svofski/videoconditioner/src/fir/filter/filter_0002_rtl.vhd

----------------------------------------------------------------------------- 
-- Altera DSP Builder Advanced Flow Tools Release Version 13.0sp1
-- Quartus II development tool and MATLAB/Simulink Interface
-- 
-- Legal Notice: Copyright 2013 Altera Corporation.  All rights reserved.    
-- Your use of  Altera  Corporation's design tools,  logic functions and other 
-- software and tools,  and its AMPP  partner logic functions, and  any output 
-- files  any of the  foregoing  device programming or simulation files),  and 
-- any associated  documentation or information are expressly subject  to  the 
-- terms and conditions  of the Altera Program License Subscription Agreement, 
-- Altera  MegaCore  Function  License  Agreement, or other applicable license 
-- agreement,  including,  without limitation,  that your use  is for the sole 
-- purpose of  programming  logic  devices  manufactured by Altera and sold by 
-- Altera or its authorized  distributors.  Please  refer  to  the  applicable 
-- agreement for further details.
----------------------------------------------------------------------------- 

-- VHDL created from filter_0002_rtl
-- VHDL created on Tue Aug 05 01:28:15 2014


library IEEE;
use IEEE.std_logic_1164.all;
use IEEE.NUMERIC_STD.all;
use IEEE.MATH_REAL.all;
use std.TextIO.all;
use work.dspba_library_package.all;

LIBRARY altera_mf;
USE altera_mf.altera_mf_components.all;
LIBRARY lpm;
USE lpm.lpm_components.all;

-- Text written from d:/SJ/nightly/13.0sp1/232/w32/p4/ip/aion/src/mip_common/hw_model.cpp:1303
entity filter_0002_rtl is
    port (
        xIn_v : in std_logic_vector(0 downto 0);
        xIn_c : in std_logic_vector(7 downto 0);
        xIn_0 : in std_logic_vector(6 downto 0);
        xOut_v : out std_logic_vector(0 downto 0);
        xOut_c : out std_logic_vector(7 downto 0);
        xOut_0 : out std_logic_vector(20 downto 0);
        clk : in std_logic;
        areset : in std_logic
        );
end;

architecture normal of filter_0002_rtl is

    attribute altera_attribute : string;
    attribute altera_attribute of normal : architecture is "-name NOT_GATE_PUSH_BACK OFF; -name PHYSICAL_SYNTHESIS_REGISTER_DUPLICATION ON; -name AUTO_SHIFT_REGISTER_RECOGNITION OFF; -name MESSAGE_DISABLE 10036; -name MESSAGE_DISABLE 10037; -name MESSAGE_DISABLE 14130; -name MESSAGE_DISABLE 14320; -name MESSAGE_DISABLE 15400; -name MESSAGE_DISABLE 14130; -name MESSAGE_DISABLE 10036; -name MESSAGE_DISABLE 12020; -name MESSAGE_DISABLE 12030; -name MESSAGE_DISABLE 12010; -name MESSAGE_DISABLE 12110; -name MESSAGE_DISABLE 14320; -name MESSAGE_DISABLE 13410";

    signal GND_q : std_logic_vector (0 downto 0);
    signal VCC_q : std_logic_vector (0 downto 0);
    signal d_u0_m0_wo0_memread_q_11_q : std_logic_vector (0 downto 0);
    signal d_u0_m0_wo0_memread_q_13_q : std_logic_vector (0 downto 0);
    signal d_u0_m0_wo0_memread_q_17_q : std_logic_vector (0 downto 0);
    signal u0_m0_wo0_wi0_delayr1_q : std_logic_vector (6 downto 0);
    signal u0_m0_wo0_wi0_delayr2_q : std_logic_vector (6 downto 0);
    signal u0_m0_wo0_wi0_delayr3_q : std_logic_vector (6 downto 0);
    signal u0_m0_wo0_wi0_delayr4_q : std_logic_vector (6 downto 0);
    signal d_u0_m0_wo0_wi0_delayr4_q_16_q : std_logic_vector (6 downto 0);
    signal u0_m0_wo0_wi0_delayr5_q : std_logic_vector (6 downto 0);
    signal d_u0_m0_wo0_wi0_delayr5_q_14_q : std_logic_vector (6 downto 0);
    signal u0_m0_wo0_wi0_delayr6_q : std_logic_vector (6 downto 0);
    signal d_u0_m0_wo0_wi0_delayr6_q_14_q : std_logic_vector (6 downto 0);
    signal u0_m0_wo0_wi0_delayr7_q : std_logic_vector (6 downto 0);
    signal d_u0_m0_wo0_wi0_delayr7_q_14_q : std_logic_vector (6 downto 0);
    signal u0_m0_wo0_wi0_delayr8_q : std_logic_vector (6 downto 0);
    signal d_u0_m0_wo0_wi0_delayr8_q_13_q : std_logic_vector (6 downto 0);
    signal u0_m0_wo0_wi0_delayr9_q : std_logic_vector (6 downto 0);
    signal d_u0_m0_wo0_wi0_delayr9_q_11_q : std_logic_vector (6 downto 0);
    signal u0_m0_wo0_wi0_delayr10_q : std_logic_vector (6 downto 0);
    signal d_u0_m0_wo0_wi0_delayr10_q_11_q : std_logic_vector (6 downto 0);
    signal u0_m0_wo0_wi0_delayr11_q : std_logic_vector (6 downto 0);
    signal d_u0_m0_wo0_wi0_delayr11_q_11_q : std_logic_vector (6 downto 0);
    signal u0_m0_wo0_wi0_delayr12_q : std_logic_vector (6 downto 0);
    signal d_u0_m0_wo0_wi0_delayr12_q_11_q : std_logic_vector (6 downto 0);
    signal u0_m0_wo0_wi0_delayr13_q : std_logic_vector (6 downto 0);
    signal d_u0_m0_wo0_wi0_delayr13_q_11_q : std_logic_vector (6 downto 0);
    signal u0_m0_wo0_wi0_delayr14_q : std_logic_vector (6 downto 0);
    signal u0_m0_wo0_wi0_delayr15_q : std_logic_vector (6 downto 0);
    signal d_u0_m0_wo0_wi0_delayr15_q_11_q : std_logic_vector (6 downto 0);
    signal u0_m0_wo0_wi0_delayr16_q : std_logic_vector (6 downto 0);
    signal d_u0_m0_wo0_wi0_delayr16_q_11_q : std_logic_vector (6 downto 0);
    signal u0_m0_wo0_wi0_delayr17_q : std_logic_vector (6 downto 0);
    signal d_u0_m0_wo0_wi0_delayr17_q_11_q : std_logic_vector (6 downto 0);
    signal u0_m0_wo0_wi0_delayr18_q : std_logic_vector (6 downto 0);
    signal d_u0_m0_wo0_wi0_delayr18_q_11_q : std_logic_vector (6 downto 0);
    signal u0_m0_wo0_wi0_delayr19_q : std_logic_vector (6 downto 0);
    signal d_u0_m0_wo0_wi0_delayr19_q_11_q : std_logic_vector (6 downto 0);
    signal u0_m0_wo0_wi0_delayr20_q : std_logic_vector (6 downto 0);
    signal d_u0_m0_wo0_wi0_delayr20_q_11_q : std_logic_vector (6 downto 0);
    signal u0_m0_wo0_wi0_delayr21_q : std_logic_vector (6 downto 0);
    signal d_u0_m0_wo0_wi0_delayr21_q_11_q : std_logic_vector (6 downto 0);
    signal u0_m0_wo0_wi0_delayr22_q : std_logic_vector (6 downto 0);
    signal d_u0_m0_wo0_wi0_delayr22_q_11_q : std_logic_vector (6 downto 0);
    signal u0_m0_wo0_wi0_delayr23_q : std_logic_vector (6 downto 0);
    signal d_u0_m0_wo0_wi0_delayr23_q_11_q : std_logic_vector (6 downto 0);
    signal u0_m0_wo0_wi0_delayr24_q : std_logic_vector (6 downto 0);
    signal d_u0_m0_wo0_wi0_delayr24_q_11_q : std_logic_vector (6 downto 0);
    signal u0_m0_wo0_wi0_delayr25_q : std_logic_vector (6 downto 0);
    signal d_u0_m0_wo0_wi0_delayr25_q_11_q : std_logic_vector (6 downto 0);
    signal u0_m0_wo0_wi0_delayr26_q : std_logic_vector (6 downto 0);
    signal u0_m0_wo0_wi0_delayr27_q : std_logic_vector (6 downto 0);
    signal d_u0_m0_wo0_wi0_delayr27_q_11_q : std_logic_vector (6 downto 0);
    signal u0_m0_wo0_wi0_delayr28_q : std_logic_vector (6 downto 0);
    signal d_u0_m0_wo0_wi0_delayr28_q_11_q : std_logic_vector (6 downto 0);
    signal u0_m0_wo0_wi0_delayr29_q : std_logic_vector (6 downto 0);
    signal d_u0_m0_wo0_wi0_delayr29_q_11_q : std_logic_vector (6 downto 0);
    signal u0_m0_wo0_wi0_delayr30_q : std_logic_vector (6 downto 0);
    signal d_u0_m0_wo0_wi0_delayr30_q_11_q : std_logic_vector (6 downto 0);
    signal u0_m0_wo0_wi0_delayr31_q : std_logic_vector (6 downto 0);
    signal d_u0_m0_wo0_wi0_delayr31_q_11_q : std_logic_vector (6 downto 0);
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

	--u0_m0_wo0_mtree_mult1_34_shift0(BITSHIFT,187)@14
    u0_m0_wo0_mtree_mult1_34_shift0_q_int <= d_u0_m0_wo0_wi0_delayr6_q_14_q & "00";
    u0_m0_wo0_mtree_mult1_34_shift0_q <= u0_m0_wo0_mtree_mult1_34_shift0_q_int(8 downto 0);

	--u0_m0_wo0_mtree_add0_17(ADD,147)@14
    u0_m0_wo0_mtree_add0_17_a <= STD_LOGIC_VECTOR((9 downto 9 => u0_m0_wo0_mtree_mult1_34_shift0_q(8)) & u0_m0_wo0_mtree_mult1_34_shift0_q);
    u0_m0_wo0_mtree_add0_17_b <= STD_LOGIC_VECTOR((9 downto 8 => u0_m0_wo0_mtree_mult1_35_shift0_q(7)) & u0_m0_wo0_mtree_mult1_35_shift0_q);
    u0_m0_wo0_mtree_add0_17: PROCESS (clk, areset)
    BEGIN
        IF (areset = '1') THEN
            u0_m0_wo0_mtree_add0_17_o <= (others => '0');
        ELSIF(clk'EVENT AND clk = '1') THEN
            u0_m0_wo0_mtree_add0_17_o <= STD_LOGIC_VECTOR(SIGNED(u0_m0_wo0_mtree_add0_17_a) + SIGNED(u0_m0_wo0_mtree_add0_17_b));
        END IF;
    END PROCESS;
    u0_m0_wo0_mtree_add0_17_q <= u0_m0_wo0_mtree_add0_17_o(9 downto 0);


	--u0_m0_wo0_wi0_delayr7(DELAY,14)@10
    u0_m0_wo0_wi0_delayr7 : dspba_delay
    GENERIC MAP ( width => 7, depth => 1 )
    PORT MAP ( xin => u0_m0_wo0_wi0_delayr6_q, xout => u0_m0_wo0_wi0_delayr7_q, ena => xIn_v(0), clk => clk, aclr => areset );

	--d_u0_m0_wo0_wi0_delayr7_q_14(DELAY,300)@10
    d_u0_m0_wo0_wi0_delayr7_q_14 : dspba_delay
    GENERIC MAP ( width => 7, depth => 4 )
    PORT MAP ( xin => u0_m0_wo0_wi0_delayr7_q, xout => d_u0_m0_wo0_wi0_delayr7_q_14_q, clk => clk, aclr => areset );

	--u0_m0_wo0_mtree_mult1_33_shift0(BITSHIFT,188)@14
    u0_m0_wo0_mtree_mult1_33_shift0_q_int <= d_u0_m0_wo0_wi0_delayr7_q_14_q & "000";
    u0_m0_wo0_mtree_mult1_33_shift0_q <= u0_m0_wo0_mtree_mult1_33_shift0_q_int(9 downto 0);

	--u0_m0_wo0_mtree_mult1_32_shift0(BITSHIFT,189)@13
    u0_m0_wo0_mtree_mult1_32_shift0_q_int <= d_u0_m0_wo0_wi0_delayr8_q_13_q & "0";
    u0_m0_wo0_mtree_mult1_32_shift0_q <= u0_m0_wo0_mtree_mult1_32_shift0_q_int(7 downto 0);

	--u0_m0_wo0_wi0_delayr8(DELAY,15)@10
    u0_m0_wo0_wi0_delayr8 : dspba_delay
    GENERIC MAP ( width => 7, depth => 1 )
    PORT MAP ( xin => u0_m0_wo0_wi0_delayr7_q, xout => u0_m0_wo0_wi0_delayr8_q, ena => xIn_v(0), clk => clk, aclr => areset );

	--d_u0_m0_wo0_wi0_delayr8_q_13(DELAY,301)@10
    d_u0_m0_wo0_wi0_delayr8_q_13 : dspba_delay
    GENERIC MAP ( width => 7, depth => 3 )
    PORT MAP ( xin => u0_m0_wo0_wi0_delayr8_q, xout => d_u0_m0_wo0_wi0_delayr8_q_13_q, clk => clk, aclr => areset );

	--u0_m0_wo0_mtree_mult1_32_add_1(ADD,190)@13
    u0_m0_wo0_mtree_mult1_32_add_1_a <= STD_LOGIC_VECTOR((8 downto 7 => d_u0_m0_wo0_wi0_delayr8_q_13_q(6)) & d_u0_m0_wo0_wi0_delayr8_q_13_q);
    u0_m0_wo0_mtree_mult1_32_add_1_b <= STD_LOGIC_VECTOR((8 downto 8 => u0_m0_wo0_mtree_mult1_32_shift0_q(7)) & u0_m0_wo0_mtree_mult1_32_shift0_q);
    u0_m0_wo0_mtree_mult1_32_add_1: PROCESS (clk, areset)
    BEGIN
        IF (areset = '1') THEN
            u0_m0_wo0_mtree_mult1_32_add_1_o <= (others => '0');
        ELSIF(clk'EVENT AND clk = '1') THEN
            u0_m0_wo0_mtree_mult1_32_add_1_o <= STD_LOGIC_VECTOR(SIGNED(u0_m0_wo0_mtree_mult1_32_add_1_a) + SIGNED(u0_m0_wo0_mtree_mult1_32_add_1_b));
        END IF;
    END PROCESS;
    u0_m0_wo0_mtree_mult1_32_add_1_q <= u0_m0_wo0_mtree_mult1_32_add_1_o(8 downto 0);


	--u0_m0_wo0_mtree_mult1_32_shift2(BITSHIFT,191)@14
    u0_m0_wo0_mtree_mult1_32_shift2_q_int <= u0_m0_wo0_mtree_mult1_32_add_1_q & "00";
    u0_m0_wo0_mtree_mult1_32_shift2_q <= u0_m0_wo0_mtree_mult1_32_shift2_q_int(10 downto 0);

	--u0_m0_wo0_mtree_add0_16(ADD,146)@14
    u0_m0_wo0_mtree_add0_16_a <= STD_LOGIC_VECTOR((11 downto 11 => u0_m0_wo0_mtree_mult1_32_shift2_q(10)) & u0_m0_wo0_mtree_mult1_32_shift2_q);
    u0_m0_wo0_mtree_add0_16_b <= STD_LOGIC_VECTOR((11 downto 10 => u0_m0_wo0_mtree_mult1_33_shift0_q(9)) & u0_m0_wo0_mtree_mult1_33_shift0_q);
    u0_m0_wo0_mtree_add0_16: PROCESS (clk, areset)
    BEGIN
        IF (areset = '1') THEN
            u0_m0_wo0_mtree_add0_16_o <= (others => '0');
        ELSIF(clk'EVENT AND clk = '1') THEN
            u0_m0_wo0_mtree_add0_16_o <= STD_LOGIC_VECTOR(SIGNED(u0_m0_wo0_mtree_add0_16_a) + SIGNED(u0_m0_wo0_mtree_add0_16_b));
        END IF;
    END PROCESS;
    u0_m0_wo0_mtree_add0_16_q <= u0_m0_wo0_mtree_add0_16_o(11 downto 0);


	--u0_m0_wo0_mtree_add1_8(ADD,158)@15
    u0_m0_wo0_mtree_add1_8_a <= STD_LOGIC_VECTOR((13 downto 12 => u0_m0_wo0_mtree_add0_16_q(11)) & u0_m0_wo0_mtree_add0_16_q);
    u0_m0_wo0_mtree_add1_8_b <= STD_LOGIC_VECTOR((13 downto 10 => u0_m0_wo0_mtree_add0_17_q(9)) & u0_m0_wo0_mtree_add0_17_q);
    u0_m0_wo0_mtree_add1_8: PROCESS (clk, areset)
    BEGIN
        IF (areset = '1') THEN
            u0_m0_wo0_mtree_add1_8_o <= (others => '0');
        ELSIF(clk'EVENT AND clk = '1') THEN
            u0_m0_wo0_mtree_add1_8_o <= STD_LOGIC_VECTOR(SIGNED(u0_m0_wo0_mtree_add1_8_a) + SIGNED(u0_m0_wo0_mtree_add1_8_b));
        END IF;
    END PROCESS;
    u0_m0_wo0_mtree_add1_8_q <= u0_m0_wo0_mtree_add1_8_o(13 downto 0);


	--u0_m0_wo0_mtree_add2_4(ADD,164)@16
    u0_m0_wo0_mtree_add2_4_a <= STD_LOGIC_VECTOR((14 downto 14 => u0_m0_wo0_mtree_add1_8_q(13)) & u0_m0_wo0_mtree_add1_8_q);
    u0_m0_wo0_mtree_add2_4_b <= STD_LOGIC_VECTOR((14 downto 7 => d_u0_m0_wo0_wi0_delayr4_q_16_q(6)) & d_u0_m0_wo0_wi0_delayr4_q_16_q);
    u0_m0_wo0_mtree_add2_4: PROCESS (clk, areset)
    BEGIN
        IF (areset = '1') THEN
            u0_m0_wo0_mtree_add2_4_o <= (others => '0');
        ELSIF(clk'EVENT AND clk = '1') THEN
            u0_m0_wo0_mtree_add2_4_o <= STD_LOGIC_VECTOR(SIGNED(u0_m0_wo0_mtree_add2_4_a) + SIGNED(u0_m0_wo0_mtree_add2_4_b));
        END IF;
    END PROCESS;
    u0_m0_wo0_mtree_add2_4_q <= u0_m0_wo0_mtree_add2_4_o(14 downto 0);


	--u0_m0_wo0_wi0_delayr9(DELAY,16)@10
    u0_m0_wo0_wi0_delayr9 : dspba_delay
    GENERIC MAP ( width => 7, depth => 1 )
    PORT MAP ( xin => u0_m0_wo0_wi0_delayr8_q, xout => u0_m0_wo0_wi0_delayr9_q, ena => xIn_v(0), clk => clk, aclr => areset );

	--d_u0_m0_wo0_wi0_delayr9_q_11(DELAY,302)@10
    d_u0_m0_wo0_wi0_delayr9_q_11 : dspba_delay
    GENERIC MAP ( width => 7, depth => 1 )
    PORT MAP ( xin => u0_m0_wo0_wi0_delayr9_q, xout => d_u0_m0_wo0_wi0_delayr9_q_11_q, clk => clk, aclr => areset );

	--u0_m0_wo0_mtree_mult1_31_shift2(BITSHIFT,194)@11
    u0_m0_wo0_mtree_mult1_31_shift2_q_int <= d_u0_m0_wo0_wi0_delayr9_q_11_q & "0000";
    u0_m0_wo0_mtree_mult1_31_shift2_q <= u0_m0_wo0_mtree_mult1_31_shift2_q_int(10 downto 0);

	--u0_m0_wo0_mtree_mult1_31_shift0(BITSHIFT,192)@10
    u0_m0_wo0_mtree_mult1_31_shift0_q_int <= u0_m0_wo0_wi0_delayr9_q & "0";
    u0_m0_wo0_mtree_mult1_31_shift0_q <= u0_m0_wo0_mtree_mult1_31_shift0_q_int(7 downto 0);

	--u0_m0_wo0_mtree_mult1_31_add_1(ADD,193)@10
    u0_m0_wo0_mtree_mult1_31_add_1_a <= STD_LOGIC_VECTOR((8 downto 7 => u0_m0_wo0_wi0_delayr9_q(6)) & u0_m0_wo0_wi0_delayr9_q);
    u0_m0_wo0_mtree_mult1_31_add_1_b <= STD_LOGIC_VECTOR((8 downto 8 => u0_m0_wo0_mtree_mult1_31_shift0_q(7)) & u0_m0_wo0_mtree_mult1_31_shift0_q);
    u0_m0_wo0_mtree_mult1_31_add_1: PROCESS (clk, areset)
    BEGIN
        IF (areset = '1') THEN
            u0_m0_wo0_mtree_mult1_31_add_1_o <= (others => '0');
        ELSIF(clk'EVENT AND clk = '1') THEN
            u0_m0_wo0_mtree_mult1_31_add_1_o <= STD_LOGIC_VECTOR(SIGNED(u0_m0_wo0_mtree_mult1_31_add_1_a) + SIGNED(u0_m0_wo0_mtree_mult1_31_add_1_b));
        END IF;
    END PROCESS;
    u0_m0_wo0_mtree_mult1_31_add_1_q <= u0_m0_wo0_mtree_mult1_31_add_1_o(8 downto 0);


	--u0_m0_wo0_mtree_mult1_31_add_3(ADD,195)@11
    u0_m0_wo0_mtree_mult1_31_add_3_a <= STD_LOGIC_VECTOR((11 downto 9 => u0_m0_wo0_mtree_mult1_31_add_1_q(8)) & u0_m0_wo0_mtree_mult1_31_add_1_q);
    u0_m0_wo0_mtree_mult1_31_add_3_b <= STD_LOGIC_VECTOR((11 downto 11 => u0_m0_wo0_mtree_mult1_31_shift2_q(10)) & u0_m0_wo0_mtree_mult1_31_shift2_q);
    u0_m0_wo0_mtree_mult1_31_add_3: PROCESS (clk, areset)
    BEGIN
        IF (areset = '1') THEN
            u0_m0_wo0_mtree_mult1_31_add_3_o <= (others => '0');
        ELSIF(clk'EVENT AND clk = '1') THEN
            u0_m0_wo0_mtree_mult1_31_add_3_o <= STD_LOGIC_VECTOR(SIGNED(u0_m0_wo0_mtree_mult1_31_add_3_a) + SIGNED(u0_m0_wo0_mtree_mult1_31_add_3_b));
        END IF;
    END PROCESS;
    u0_m0_wo0_mtree_mult1_31_add_3_q <= u0_m0_wo0_mtree_mult1_31_add_3_o(11 downto 0);


	--u0_m0_wo0_mtree_mult1_30_shift0(BITSHIFT,196)@10
    u0_m0_wo0_mtree_mult1_30_shift0_q_int <= u0_m0_wo0_wi0_delayr10_q & "00";
    u0_m0_wo0_mtree_mult1_30_shift0_q <= u0_m0_wo0_mtree_mult1_30_shift0_q_int(8 downto 0);

	--u0_m0_wo0_wi0_delayr10(DELAY,17)@10
    u0_m0_wo0_wi0_delayr10 : dspba_delay
    GENERIC MAP ( width => 7, depth => 1 )
    PORT MAP ( xin => u0_m0_wo0_wi0_delayr9_q, xout => u0_m0_wo0_wi0_delayr10_q, ena => xIn_v(0), clk => clk, aclr => areset );

	--u0_m0_wo0_mtree_mult1_30_add_1(ADD,197)@10
    u0_m0_wo0_mtree_mult1_30_add_1_a <= STD_LOGIC_VECTOR((9 downto 7 => u0_m0_wo0_wi0_delayr10_q(6)) & u0_m0_wo0_wi0_delayr10_q);
    u0_m0_wo0_mtree_mult1_30_add_1_b <= STD_LOGIC_VECTOR((9 downto 9 => u0_m0_wo0_mtree_mult1_30_shift0_q(8)) & u0_m0_wo0_mtree_mult1_30_shift0_q);
    u0_m0_wo0_mtree_mult1_30_add_1: PROCESS (clk, areset)
    BEGIN
        IF (areset = '1') THEN
            u0_m0_wo0_mtree_mult1_30_add_1_o <= (others => '0');
        ELSIF(clk'EVENT AND clk = '1') THEN
            u0_m0_wo0_mtree_mult1_30_add_1_o <= STD_LOGIC_VECTOR(SIGNED(u0_m0_wo0_mtree_mult1_30_add_1_a) + SIGNED(u0_m0_wo0_mtree_mult1_30_add_1_b));
        END IF;
    END PROCESS;
    u0_m0_wo0_mtree_mult1_30_add_1_q <= u0_m0_wo0_mtree_mult1_30_add_1_o(9 downto 0);


	--d_u0_m0_wo0_wi0_delayr10_q_11(DELAY,303)@10
    d_u0_m0_wo0_wi0_delayr10_q_11 : dspba_delay
    GENERIC MAP ( width => 7, depth => 1 )
    PORT MAP ( xin => u0_m0_wo0_wi0_delayr10_q, xout => d_u0_m0_wo0_wi0_delayr10_q_11_q, clk => clk, aclr => areset );

	--u0_m0_wo0_mtree_mult1_30_shift2(BITSHIFT,198)@11
    u0_m0_wo0_mtree_mult1_30_shift2_q_int <= d_u0_m0_wo0_wi0_delayr10_q_11_q & "00000";
    u0_m0_wo0_mtree_mult1_30_shift2_q <= u0_m0_wo0_mtree_mult1_30_shift2_q_int(11 downto 0);

	--u0_m0_wo0_mtree_mult1_30_sub_3(SUB,199)@11
    u0_m0_wo0_mtree_mult1_30_sub_3_a <= STD_LOGIC_VECTOR((12 downto 12 => u0_m0_wo0_mtree_mult1_30_shift2_q(11)) & u0_m0_wo0_mtree_mult1_30_shift2_q);
    u0_m0_wo0_mtree_mult1_30_sub_3_b <= STD_LOGIC_VECTOR((12 downto 10 => u0_m0_wo0_mtree_mult1_30_add_1_q(9)) & u0_m0_wo0_mtree_mult1_30_add_1_q);
    u0_m0_wo0_mtree_mult1_30_sub_3: PROCESS (clk, areset)
    BEGIN
        IF (areset = '1') THEN
            u0_m0_wo0_mtree_mult1_30_sub_3_o <= (others => '0');
        ELSIF(clk'EVENT AND clk = '1') THEN
            u0_m0_wo0_mtree_mult1_30_sub_3_o <= STD_LOGIC_VECTOR(SIGNED(u0_m0_wo0_mtree_mult1_30_sub_3_a) - SIGNED(u0_m0_wo0_mtree_mult1_30_sub_3_b));
        END IF;
    END PROCESS;
    u0_m0_wo0_mtree_mult1_30_sub_3_q <= u0_m0_wo0_mtree_mult1_30_sub_3_o(12 downto 0);


	--u0_m0_wo0_mtree_add0_15(ADD,145)@12
    u0_m0_wo0_mtree_add0_15_a <= STD_LOGIC_VECTOR((13 downto 13 => u0_m0_wo0_mtree_mult1_30_sub_3_q(12)) & u0_m0_wo0_mtree_mult1_30_sub_3_q);
    u0_m0_wo0_mtree_add0_15_b <= STD_LOGIC_VECTOR((13 downto 12 => u0_m0_wo0_mtree_mult1_31_add_3_q(11)) & u0_m0_wo0_mtree_mult1_31_add_3_q);
    u0_m0_wo0_mtree_add0_15: PROCESS (clk, areset)
    BEGIN
        IF (areset = '1') THEN
            u0_m0_wo0_mtree_add0_15_o <= (others => '0');
        ELSIF(clk'EVENT AND clk = '1') THEN
            u0_m0_wo0_mtree_add0_15_o <= STD_LOGIC_VECTOR(SIGNED(u0_m0_wo0_mtree_add0_15_a) + SIGNED(u0_m0_wo0_mtree_add0_15_b));
        END IF;
    END PROCESS;
    u0_m0_wo0_mtree_add0_15_q <= u0_m0_wo0_mtree_add0_15_o(13 downto 0);


	--u0_m0_wo0_wi0_delayr11(DELAY,18)@10
    u0_m0_wo0_wi0_delayr11 : dspba_delay
    GENERIC MAP ( width => 7, depth => 1 )
    PORT MAP ( xin => u0_m0_wo0_wi0_delayr10_q, xout => u0_m0_wo0_wi0_delayr11_q, ena => xIn_v(0), clk => clk, aclr => areset );

	--d_u0_m0_wo0_wi0_delayr11_q_11(DELAY,304)@10
    d_u0_m0_wo0_wi0_delayr11_q_11 : dspba_delay
    GENERIC MAP ( width => 7, depth => 1 )
    PORT MAP ( xin => u0_m0_wo0_wi0_delayr11_q, xout => d_u0_m0_wo0_wi0_delayr11_q_11_q, clk => clk, aclr => areset );

	--u0_m0_wo0_mtree_mult1_29_shift2(BITSHIFT,202)@11
    u0_m0_wo0_mtree_mult1_29_shift2_q_int <= d_u0_m0_wo0_wi0_delayr11_q_11_q & "00000";
    u0_m0_wo0_mtree_mult1_29_shift2_q <= u0_m0_wo0_mtree_mult1_29_shift2_q_int(11 downto 0);

	--u0_m0_wo0_mtree_mult1_29_shift0(BITSHIFT,200)@10
    u0_m0_wo0_mtree_mult1_29_shift0_q_int <= u0_m0_wo0_wi0_delayr11_q & "00";
    u0_m0_wo0_mtree_mult1_29_shift0_q <= u0_m0_wo0_mtree_mult1_29_shift0_q_int(8 downto 0);

	--u0_m0_wo0_mtree_mult1_29_add_1(ADD,201)@10
    u0_m0_wo0_mtree_mult1_29_add_1_a <= STD_LOGIC_VECTOR((9 downto 7 => u0_m0_wo0_wi0_delayr11_q(6)) & u0_m0_wo0_wi0_delayr11_q);
    u0_m0_wo0_mtree_mult1_29_add_1_b <= STD_LOGIC_VECTOR((9 downto 9 => u0_m0_wo0_mtree_mult1_29_shift0_q(8)) & u0_m0_wo0_mtree_mult1_29_shift0_q);
    u0_m0_wo0_mtree_mult1_29_add_1: PROCESS (clk, areset)
    BEGIN
        IF (areset = '1') THEN
            u0_m0_wo0_mtree_mult1_29_add_1_o <= (others => '0');
        ELSIF(clk'EVENT AND clk = '1') THEN
            u0_m0_wo0_mtree_mult1_29_add_1_o <= STD_LOGIC_VECTOR(SIGNED(u0_m0_wo0_mtree_mult1_29_add_1_a) + SIGNED(u0_m0_wo0_mtree_mult1_29_add_1_b));
        END IF;
    END PROCESS;
    u0_m0_wo0_mtree_mult1_29_add_1_q <= u0_m0_wo0_mtree_mult1_29_add_1_o(9 downto 0);


	--u0_m0_wo0_mtree_mult1_29_add_3(ADD,203)@11
    u0_m0_wo0_mtree_mult1_29_add_3_a <= STD_LOGIC_VECTOR((12 downto 10 => u0_m0_wo0_mtree_mult1_29_add_1_q(9)) & u0_m0_wo0_mtree_mult1_29_add_1_q);
    u0_m0_wo0_mtree_mult1_29_add_3_b <= STD_LOGIC_VECTOR((12 downto 12 => u0_m0_wo0_mtree_mult1_29_shift2_q(11)) & u0_m0_wo0_mtree_mult1_29_shift2_q);
    u0_m0_wo0_mtree_mult1_29_add_3: PROCESS (clk, areset)
    BEGIN
        IF (areset = '1') THEN
            u0_m0_wo0_mtree_mult1_29_add_3_o <= (others => '0');
        ELSIF(clk'EVENT AND clk = '1') THEN
            u0_m0_wo0_mtree_mult1_29_add_3_o <= STD_LOGIC_VECTOR(SIGNED(u0_m0_wo0_mtree_mult1_29_add_3_a) + SIGNED(u0_m0_wo0_mtree_mult1_29_add_3_b));
        END IF;
    END PROCESS;
    u0_m0_wo0_mtree_mult1_29_add_3_q <= u0_m0_wo0_mtree_mult1_29_add_3_o(12 downto 0);


	--u0_m0_wo0_mtree_mult1_28_shift0(BITSHIFT,204)@11
    u0_m0_wo0_mtree_mult1_28_shift0_q_int <= d_u0_m0_wo0_wi0_delayr12_q_11_q & "0";
    u0_m0_wo0_mtree_mult1_28_shift0_q <= u0_m0_wo0_mtree_mult1_28_shift0_q_int(7 downto 0);

	--u0_m0_wo0_wi0_delayr12(DELAY,19)@10
    u0_m0_wo0_wi0_delayr12 : dspba_delay
    GENERIC MAP ( width => 7, depth => 1 )
    PORT MAP ( xin => u0_m0_wo0_wi0_delayr11_q, xout => u0_m0_wo0_wi0_delayr12_q, ena => xIn_v(0), clk => clk, aclr => areset );

	--d_u0_m0_wo0_wi0_delayr12_q_11(DELAY,305)@10
    d_u0_m0_wo0_wi0_delayr12_q_11 : dspba_delay
    GENERIC MAP ( width => 7, depth => 1 )
    PORT MAP ( xin => u0_m0_wo0_wi0_delayr12_q, xout => d_u0_m0_wo0_wi0_delayr12_q_11_q, clk => clk, aclr => areset );

	--u0_m0_wo0_mtree_mult1_28_add_1(ADD,205)@11
    u0_m0_wo0_mtree_mult1_28_add_1_a <= STD_LOGIC_VECTOR((8 downto 7 => d_u0_m0_wo0_wi0_delayr12_q_11_q(6)) & d_u0_m0_wo0_wi0_delayr12_q_11_q);
    u0_m0_wo0_mtree_mult1_28_add_1_b <= STD_LOGIC_VECTOR((8 downto 8 => u0_m0_wo0_mtree_mult1_28_shift0_q(7)) & u0_m0_wo0_mtree_mult1_28_shift0_q);
    u0_m0_wo0_mtree_mult1_28_add_1: PROCESS (clk, areset)
    BEGIN
        IF (areset = '1') THEN
            u0_m0_wo0_mtree_mult1_28_add_1_o <= (others => '0');
        ELSIF(clk'EVENT AND clk = '1') THEN
            u0_m0_wo0_mtree_mult1_28_add_1_o <= STD_LOGIC_VECTOR(SIGNED(u0_m0_wo0_mtree_mult1_28_add_1_a) + SIGNED(u0_m0_wo0_mtree_mult1_28_add_1_b));
        END IF;
    END PROCESS;
    u0_m0_wo0_mtree_mult1_28_add_1_q <= u0_m0_wo0_mtree_mult1_28_add_1_o(8 downto 0);


	--u0_m0_wo0_mtree_mult1_28_shift2(BITSHIFT,206)@12
    u0_m0_wo0_mtree_mult1_28_shift2_q_int <= u0_m0_wo0_mtree_mult1_28_add_1_q & "0000";
    u0_m0_wo0_mtree_mult1_28_shift2_q <= u0_m0_wo0_mtree_mult1_28_shift2_q_int(12 downto 0);

	--u0_m0_wo0_mtree_add0_14(ADD,144)@12
    u0_m0_wo0_mtree_add0_14_a <= STD_LOGIC_VECTOR((13 downto 13 => u0_m0_wo0_mtree_mult1_28_shift2_q(12)) & u0_m0_wo0_mtree_mult1_28_shift2_q);
    u0_m0_wo0_mtree_add0_14_b <= STD_LOGIC_VECTOR((13 downto 13 => u0_m0_wo0_mtree_mult1_29_add_3_q(12)) & u0_m0_wo0_mtree_mult1_29_add_3_q);
    u0_m0_wo0_mtree_add0_14: PROCESS (clk, areset)
    BEGIN
        IF (areset = '1') THEN
            u0_m0_wo0_mtree_add0_14_o <= (others => '0');
        ELSIF(clk'EVENT AND clk = '1') THEN
            u0_m0_wo0_mtree_add0_14_o <= STD_LOGIC_VECTOR(SIGNED(u0_m0_wo0_mtree_add0_14_a) + SIGNED(u0_m0_wo0_mtree_add0_14_b));
        END IF;
    END PROCESS;
    u0_m0_wo0_mtree_add0_14_q <= u0_m0_wo0_mtree_add0_14_o(13 downto 0);


	--u0_m0_wo0_mtree_add1_7(ADD,157)@13
    u0_m0_wo0_mtree_add1_7_a <= STD_LOGIC_VECTOR((15 downto 14 => u0_m0_wo0_mtree_add0_14_q(13)) & u0_m0_wo0_mtree_add0_14_q);
    u0_m0_wo0_mtree_add1_7_b <= STD_LOGIC_VECTOR((15 downto 14 => u0_m0_wo0_mtree_add0_15_q(13)) & u0_m0_wo0_mtree_add0_15_q);
    u0_m0_wo0_mtree_add1_7: PROCESS (clk, areset)
    BEGIN
        IF (areset = '1') THEN
            u0_m0_wo0_mtree_add1_7_o <= (others => '0');
        ELSIF(clk'EVENT AND clk = '1') THEN
            u0_m0_wo0_mtree_add1_7_o <= STD_LOGIC_VECTOR(SIGNED(u0_m0_wo0_mtree_add1_7_a) + SIGNED(u0_m0_wo0_mtree_add1_7_b));
        END IF;
    END PROCESS;
    u0_m0_wo0_mtree_add1_7_q <= u0_m0_wo0_mtree_add1_7_o(15 downto 0);


	--u0_m0_wo0_wi0_delayr13(DELAY,20)@10
    u0_m0_wo0_wi0_delayr13 : dspba_delay
    GENERIC MAP ( width => 7, depth => 1 )
    PORT MAP ( xin => u0_m0_wo0_wi0_delayr12_q, xout => u0_m0_wo0_wi0_delayr13_q, ena => xIn_v(0), clk => clk, aclr => areset );

	--d_u0_m0_wo0_wi0_delayr13_q_11(DELAY,306)@10
    d_u0_m0_wo0_wi0_delayr13_q_11 : dspba_delay
    GENERIC MAP ( width => 7, depth => 1 )
    PORT MAP ( xin => u0_m0_wo0_wi0_delayr13_q, xout => d_u0_m0_wo0_wi0_delayr13_q_11_q, clk => clk, aclr => areset );

	--u0_m0_wo0_mtree_mult1_27_shift2(BITSHIFT,209)@11
    u0_m0_wo0_mtree_mult1_27_shift2_q_int <= d_u0_m0_wo0_wi0_delayr13_q_11_q & "000000";
    u0_m0_wo0_mtree_mult1_27_shift2_q <= u0_m0_wo0_mtree_mult1_27_shift2_q_int(12 downto 0);

	--u0_m0_wo0_mtree_mult1_27_shift0(BITSHIFT,207)@10
    u0_m0_wo0_mtree_mult1_27_shift0_q_int <= u0_m0_wo0_wi0_delayr13_q & "00";
    u0_m0_wo0_mtree_mult1_27_shift0_q <= u0_m0_wo0_mtree_mult1_27_shift0_q_int(8 downto 0);

	--u0_m0_wo0_mtree_mult1_27_sub_1(SUB,208)@10
    u0_m0_wo0_mtree_mult1_27_sub_1_a <= STD_LOGIC_VECTOR((9 downto 7 => u0_m0_wo0_wi0_delayr13_q(6)) & u0_m0_wo0_wi0_delayr13_q);
    u0_m0_wo0_mtree_mult1_27_sub_1_b <= STD_LOGIC_VECTOR((9 downto 9 => u0_m0_wo0_mtree_mult1_27_shift0_q(8)) & u0_m0_wo0_mtree_mult1_27_shift0_q);
    u0_m0_wo0_mtree_mult1_27_sub_1: PROCESS (clk, areset)
    BEGIN
        IF (areset = '1') THEN
            u0_m0_wo0_mtree_mult1_27_sub_1_o <= (others => '0');
        ELSIF(clk'EVENT AND clk = '1') THEN
            u0_m0_wo0_mtree_mult1_27_sub_1_o <= STD_LOGIC_VECTOR(SIGNED(u0_m0_wo0_mtree_mult1_27_sub_1_a) - SIGNED(u0_m0_wo0_mtree_mult1_27_sub_1_b));
        END IF;
    END PROCESS;
    u0_m0_wo0_mtree_mult1_27_sub_1_q <= u0_m0_wo0_mtree_mult1_27_sub_1_o(9 downto 0);


	--u0_m0_wo0_mtree_mult1_27_add_3(ADD,210)@11
    u0_m0_wo0_mtree_mult1_27_add_3_a <= STD_LOGIC_VECTOR((13 downto 10 => u0_m0_wo0_mtree_mult1_27_sub_1_q(9)) & u0_m0_wo0_mtree_mult1_27_sub_1_q);
    u0_m0_wo0_mtree_mult1_27_add_3_b <= STD_LOGIC_VECTOR((13 downto 13 => u0_m0_wo0_mtree_mult1_27_shift2_q(12)) & u0_m0_wo0_mtree_mult1_27_shift2_q);
    u0_m0_wo0_mtree_mult1_27_add_3: PROCESS (clk, areset)
    BEGIN
        IF (areset = '1') THEN
            u0_m0_wo0_mtree_mult1_27_add_3_o <= (others => '0');
        ELSIF(clk'EVENT AND clk = '1') THEN
            u0_m0_wo0_mtree_mult1_27_add_3_o <= STD_LOGIC_VECTOR(SIGNED(u0_m0_wo0_mtree_mult1_27_add_3_a) + SIGNED(u0_m0_wo0_mtree_mult1_27_add_3_b));
        END IF;
    END PROCESS;
    u0_m0_wo0_mtree_mult1_27_add_3_q <= u0_m0_wo0_mtree_mult1_27_add_3_o(13 downto 0);


	--u0_m0_wo0_mtree_mult1_26_shift2(BITSHIFT,213)@10
    u0_m0_wo0_mtree_mult1_26_shift2_q_int <= u0_m0_wo0_wi0_delayr14_q & "000";
    u0_m0_wo0_mtree_mult1_26_shift2_q <= u0_m0_wo0_mtree_mult1_26_shift2_q_int(9 downto 0);

	--u0_m0_wo0_wi0_delayr14(DELAY,21)@10
    u0_m0_wo0_wi0_delayr14 : dspba_delay
    GENERIC MAP ( width => 7, depth => 1 )
    PORT MAP ( xin => u0_m0_wo0_wi0_delayr13_q, xout => u0_m0_wo0_wi0_delayr14_q, ena => xIn_v(0), clk => clk, aclr => areset );

	--u0_m0_wo0_mtree_mult1_26_add_3(ADD,214)@10
    u0_m0_wo0_mtree_mult1_26_add_3_a <= STD_LOGIC_VECTOR((10 downto 7 => u0_m0_wo0_wi0_delayr14_q(6)) & u0_m0_wo0_wi0_delayr14_q);
    u0_m0_wo0_mtree_mult1_26_add_3_b <= STD_LOGIC_VECTOR((10 downto 10 => u0_m0_wo0_mtree_mult1_26_shift2_q(9)) & u0_m0_wo0_mtree_mult1_26_shift2_q);
    u0_m0_wo0_mtree_mult1_26_add_3: PROCESS (clk, areset)
    BEGIN
        IF (areset = '1') THEN
            u0_m0_wo0_mtree_mult1_26_add_3_o <= (others => '0');
        ELSIF(clk'EVENT AND clk = '1') THEN
            u0_m0_wo0_mtree_mult1_26_add_3_o <= STD_LOGIC_VECTOR(SIGNED(u0_m0_wo0_mtree_mult1_26_add_3_a) + SIGNED(u0_m0_wo0_mtree_mult1_26_add_3_b));
        END IF;
    END PROCESS;
    u0_m0_wo0_mtree_mult1_26_add_3_q <= u0_m0_wo0_mtree_mult1_26_add_3_o(10 downto 0);


	--u0_m0_wo0_mtree_mult1_26_shift4(BITSHIFT,215)@11
    u0_m0_wo0_mtree_mult1_26_shift4_q_int <= u0_m0_wo0_mtree_mult1_26_add_3_q & "000";
    u0_m0_wo0_mtree_mult1_26_shift4_q <= u0_m0_wo0_mtree_mult1_26_shift4_q_int(13 downto 0);

	--u0_m0_wo0_mtree_mult1_26_shift0(BITSHIFT,211)@10
    u0_m0_wo0_mtree_mult1_26_shift0_q_int <= u0_m0_wo0_wi0_delayr14_q & "0";
    u0_m0_wo0_mtree_mult1_26_shift0_q <= u0_m0_wo0_mtree_mult1_26_shift0_q_int(7 downto 0);

	--u0_m0_wo0_mtree_mult1_26_add_1(ADD,212)@10
    u0_m0_wo0_mtree_mult1_26_add_1_a <= STD_LOGIC_VECTOR((8 downto 7 => u0_m0_wo0_wi0_delayr14_q(6)) & u0_m0_wo0_wi0_delayr14_q);
    u0_m0_wo0_mtree_mult1_26_add_1_b <= STD_LOGIC_VECTOR((8 downto 8 => u0_m0_wo0_mtree_mult1_26_shift0_q(7)) & u0_m0_wo0_mtree_mult1_26_shift0_q);
    u0_m0_wo0_mtree_mult1_26_add_1: PROCESS (clk, areset)
    BEGIN
        IF (areset = '1') THEN
            u0_m0_wo0_mtree_mult1_26_add_1_o <= (others => '0');
        ELSIF(clk'EVENT AND clk = '1') THEN
            u0_m0_wo0_mtree_mult1_26_add_1_o <= STD_LOGIC_VECTOR(SIGNED(u0_m0_wo0_mtree_mult1_26_add_1_a) + SIGNED(u0_m0_wo0_mtree_mult1_26_add_1_b));
        END IF;
    END PROCESS;
    u0_m0_wo0_mtree_mult1_26_add_1_q <= u0_m0_wo0_mtree_mult1_26_add_1_o(8 downto 0);


	--u0_m0_wo0_mtree_mult1_26_add_5(ADD,216)@11
    u0_m0_wo0_mtree_mult1_26_add_5_a <= STD_LOGIC_VECTOR((14 downto 9 => u0_m0_wo0_mtree_mult1_26_add_1_q(8)) & u0_m0_wo0_mtree_mult1_26_add_1_q);
    u0_m0_wo0_mtree_mult1_26_add_5_b <= STD_LOGIC_VECTOR((14 downto 14 => u0_m0_wo0_mtree_mult1_26_shift4_q(13)) & u0_m0_wo0_mtree_mult1_26_shift4_q);
    u0_m0_wo0_mtree_mult1_26_add_5: PROCESS (clk, areset)
    BEGIN
        IF (areset = '1') THEN
            u0_m0_wo0_mtree_mult1_26_add_5_o <= (others => '0');
        ELSIF(clk'EVENT AND clk = '1') THEN
            u0_m0_wo0_mtree_mult1_26_add_5_o <= STD_LOGIC_VECTOR(SIGNED(u0_m0_wo0_mtree_mult1_26_add_5_a) + SIGNED(u0_m0_wo0_mtree_mult1_26_add_5_b));
        END IF;
    END PROCESS;
    u0_m0_wo0_mtree_mult1_26_add_5_q <= u0_m0_wo0_mtree_mult1_26_add_5_o(14 downto 0);


	--u0_m0_wo0_mtree_add0_13(ADD,143)@12
    u0_m0_wo0_mtree_add0_13_a <= STD_LOGIC_VECTOR((15 downto 15 => u0_m0_wo0_mtree_mult1_26_add_5_q(14)) & u0_m0_wo0_mtree_mult1_26_add_5_q);
    u0_m0_wo0_mtree_add0_13_b <= STD_LOGIC_VECTOR((15 downto 14 => u0_m0_wo0_mtree_mult1_27_add_3_q(13)) & u0_m0_wo0_mtree_mult1_27_add_3_q);
    u0_m0_wo0_mtree_add0_13: PROCESS (clk, areset)
    BEGIN
        IF (areset = '1') THEN
            u0_m0_wo0_mtree_add0_13_o <= (others => '0');
        ELSIF(clk'EVENT AND clk = '1') THEN
            u0_m0_wo0_mtree_add0_13_o <= STD_LOGIC_VECTOR(SIGNED(u0_m0_wo0_mtree_add0_13_a) + SIGNED(u0_m0_wo0_mtree_add0_13_b));
        END IF;
    END PROCESS;
    u0_m0_wo0_mtree_add0_13_q <= u0_m0_wo0_mtree_add0_13_o(15 downto 0);


	--u0_m0_wo0_wi0_delayr15(DELAY,22)@10
    u0_m0_wo0_wi0_delayr15 : dspba_delay
    GENERIC MAP ( width => 7, depth => 1 )
    PORT MAP ( xin => u0_m0_wo0_wi0_delayr14_q, xout => u0_m0_wo0_wi0_delayr15_q, ena => xIn_v(0), clk => clk, aclr => areset );

	--d_u0_m0_wo0_wi0_delayr15_q_11(DELAY,307)@10
    d_u0_m0_wo0_wi0_delayr15_q_11 : dspba_delay
    GENERIC MAP ( width => 7, depth => 1 )
    PORT MAP ( xin => u0_m0_wo0_wi0_delayr15_q, xout => d_u0_m0_wo0_wi0_delayr15_q_11_q, clk => clk, aclr => areset );

	--u0_m0_wo0_mtree_mult1_25_shift2(BITSHIFT,219)@11
    u0_m0_wo0_mtree_mult1_25_shift2_q_int <= d_u0_m0_wo0_wi0_delayr15_q_11_q & "000";
    u0_m0_wo0_mtree_mult1_25_shift2_q <= u0_m0_wo0_mtree_mult1_25_shift2_q_int(9 downto 0);

	--u0_m0_wo0_mtree_mult1_25_shift0(BITSHIFT,217)@10
    u0_m0_wo0_mtree_mult1_25_shift0_q_int <= u0_m0_wo0_wi0_delayr15_q & "0";
    u0_m0_wo0_mtree_mult1_25_shift0_q <= u0_m0_wo0_mtree_mult1_25_shift0_q_int(7 downto 0);

	--u0_m0_wo0_mtree_mult1_25_add_1(ADD,218)@10
    u0_m0_wo0_mtree_mult1_25_add_1_a <= STD_LOGIC_VECTOR((8 downto 7 => u0_m0_wo0_wi0_delayr15_q(6)) & u0_m0_wo0_wi0_delayr15_q);
    u0_m0_wo0_mtree_mult1_25_add_1_b <= STD_LOGIC_VECTOR((8 downto 8 => u0_m0_wo0_mtree_mult1_25_shift0_q(7)) & u0_m0_wo0_mtree_mult1_25_shift0_q);
    u0_m0_wo0_mtree_mult1_25_add_1: PROCESS (clk, areset)
    BEGIN
        IF (areset = '1') THEN
            u0_m0_wo0_mtree_mult1_25_add_1_o <= (others => '0');
        ELSIF(clk'EVENT AND clk = '1') THEN
            u0_m0_wo0_mtree_mult1_25_add_1_o <= STD_LOGIC_VECTOR(SIGNED(u0_m0_wo0_mtree_mult1_25_add_1_a) + SIGNED(u0_m0_wo0_mtree_mult1_25_add_1_b));
        END IF;
    END PROCESS;
    u0_m0_wo0_mtree_mult1_25_add_1_q <= u0_m0_wo0_mtree_mult1_25_add_1_o(8 downto 0);


	--u0_m0_wo0_mtree_mult1_25_add_3(ADD,220)@11
    u0_m0_wo0_mtree_mult1_25_add_3_a <= STD_LOGIC_VECTOR((10 downto 9 => u0_m0_wo0_mtree_mult1_25_add_1_q(8)) & u0_m0_wo0_mtree_mult1_25_add_1_q);
    u0_m0_wo0_mtree_mult1_25_add_3_b <= STD_LOGIC_VECTOR((10 downto 10 => u0_m0_wo0_mtree_mult1_25_shift2_q(9)) & u0_m0_wo0_mtree_mult1_25_shift2_q);
    u0_m0_wo0_mtree_mult1_25_add_3: PROCESS (clk, areset)
    BEGIN
        IF (areset = '1') THEN
            u0_m0_wo0_mtree_mult1_25_add_3_o <= (others => '0');
        ELSIF(clk'EVENT AND clk = '1') THEN
            u0_m0_wo0_mtree_mult1_25_add_3_o <= STD_LOGIC_VECTOR(SIGNED(u0_m0_wo0_mtree_mult1_25_add_3_a) + SIGNED(u0_m0_wo0_mtree_mult1_25_add_3_b));
        END IF;
    END PROCESS;
    u0_m0_wo0_mtree_mult1_25_add_3_q <= u0_m0_wo0_mtree_mult1_25_add_3_o(10 downto 0);


	--u0_m0_wo0_mtree_mult1_25_shift4(BITSHIFT,221)@12
    u0_m0_wo0_mtree_mult1_25_shift4_q_int <= u0_m0_wo0_mtree_mult1_25_add_3_q & "000";
    u0_m0_wo0_mtree_mult1_25_shift4_q <= u0_m0_wo0_mtree_mult1_25_shift4_q_int(13 downto 0);

	--u0_m0_wo0_wi0_delayr16(DELAY,23)@10
    u0_m0_wo0_wi0_delayr16 : dspba_delay
    GENERIC MAP ( width => 7, depth => 1 )
    PORT MAP ( xin => u0_m0_wo0_wi0_delayr15_q, xout => u0_m0_wo0_wi0_delayr16_q, ena => xIn_v(0), clk => clk, aclr => areset );

	--d_u0_m0_wo0_wi0_delayr16_q_11(DELAY,308)@10
    d_u0_m0_wo0_wi0_delayr16_q_11 : dspba_delay
    GENERIC MAP ( width => 7, depth => 1 )
    PORT MAP ( xin => u0_m0_wo0_wi0_delayr16_q, xout => d_u0_m0_wo0_wi0_delayr16_q_11_q, clk => clk, aclr => areset );

	--u0_m0_wo0_mtree_mult1_24_shift2(BITSHIFT,224)@11
    u0_m0_wo0_mtree_mult1_24_shift2_q_int <= d_u0_m0_wo0_wi0_delayr16_q_11_q & "0000";
    u0_m0_wo0_mtree_mult1_24_shift2_q <= u0_m0_wo0_mtree_mult1_24_shift2_q_int(10 downto 0);

	--u0_m0_wo0_mtree_mult1_24_shift0(BITSHIFT,222)@10
    u0_m0_wo0_mtree_mult1_24_shift0_q_int <= u0_m0_wo0_wi0_delayr16_q & "000";
    u0_m0_wo0_mtree_mult1_24_shift0_q <= u0_m0_wo0_mtree_mult1_24_shift0_q_int(9 downto 0);

	--u0_m0_wo0_mtree_mult1_24_add_1(ADD,223)@10
    u0_m0_wo0_mtree_mult1_24_add_1_a <= STD_LOGIC_VECTOR((10 downto 7 => u0_m0_wo0_wi0_delayr16_q(6)) & u0_m0_wo0_wi0_delayr16_q);
    u0_m0_wo0_mtree_mult1_24_add_1_b <= STD_LOGIC_VECTOR((10 downto 10 => u0_m0_wo0_mtree_mult1_24_shift0_q(9)) & u0_m0_wo0_mtree_mult1_24_shift0_q);
    u0_m0_wo0_mtree_mult1_24_add_1: PROCESS (clk, areset)
    BEGIN
        IF (areset = '1') THEN
            u0_m0_wo0_mtree_mult1_24_add_1_o <= (others => '0');
        ELSIF(clk'EVENT AND clk = '1') THEN
            u0_m0_wo0_mtree_mult1_24_add_1_o <= STD_LOGIC_VECTOR(SIGNED(u0_m0_wo0_mtree_mult1_24_add_1_a) + SIGNED(u0_m0_wo0_mtree_mult1_24_add_1_b));
        END IF;
    END PROCESS;
    u0_m0_wo0_mtree_mult1_24_add_1_q <= u0_m0_wo0_mtree_mult1_24_add_1_o(10 downto 0);


	--u0_m0_wo0_mtree_mult1_24_add_3(ADD,225)@11
    u0_m0_wo0_mtree_mult1_24_add_3_a <= STD_LOGIC_VECTOR((11 downto 11 => u0_m0_wo0_mtree_mult1_24_add_1_q(10)) & u0_m0_wo0_mtree_mult1_24_add_1_q);
    u0_m0_wo0_mtree_mult1_24_add_3_b <= STD_LOGIC_VECTOR((11 downto 11 => u0_m0_wo0_mtree_mult1_24_shift2_q(10)) & u0_m0_wo0_mtree_mult1_24_shift2_q);
    u0_m0_wo0_mtree_mult1_24_add_3: PROCESS (clk, areset)
    BEGIN
        IF (areset = '1') THEN
            u0_m0_wo0_mtree_mult1_24_add_3_o <= (others => '0');
        ELSIF(clk'EVENT AND clk = '1') THEN
            u0_m0_wo0_mtree_mult1_24_add_3_o <= STD_LOGIC_VECTOR(SIGNED(u0_m0_wo0_mtree_mult1_24_add_3_a) + SIGNED(u0_m0_wo0_mtree_mult1_24_add_3_b));
        END IF;
    END PROCESS;
    u0_m0_wo0_mtree_mult1_24_add_3_q <= u0_m0_wo0_mtree_mult1_24_add_3_o(11 downto 0);


	--u0_m0_wo0_mtree_mult1_24_shift4(BITSHIFT,226)@12
    u0_m0_wo0_mtree_mult1_24_shift4_q_int <= u0_m0_wo0_mtree_mult1_24_add_3_q & "00";
    u0_m0_wo0_mtree_mult1_24_shift4_q <= u0_m0_wo0_mtree_mult1_24_shift4_q_int(13 downto 0);

	--u0_m0_wo0_mtree_add0_12(ADD,142)@12
    u0_m0_wo0_mtree_add0_12_a <= STD_LOGIC_VECTOR((14 downto 14 => u0_m0_wo0_mtree_mult1_24_shift4_q(13)) & u0_m0_wo0_mtree_mult1_24_shift4_q);
    u0_m0_wo0_mtree_add0_12_b <= STD_LOGIC_VECTOR((14 downto 14 => u0_m0_wo0_mtree_mult1_25_shift4_q(13)) & u0_m0_wo0_mtree_mult1_25_shift4_q);
    u0_m0_wo0_mtree_add0_12: PROCESS (clk, areset)
    BEGIN
        IF (areset = '1') THEN
            u0_m0_wo0_mtree_add0_12_o <= (others => '0');
        ELSIF(clk'EVENT AND clk = '1') THEN
            u0_m0_wo0_mtree_add0_12_o <= STD_LOGIC_VECTOR(SIGNED(u0_m0_wo0_mtree_add0_12_a) + SIGNED(u0_m0_wo0_mtree_add0_12_b));
        END IF;
    END PROCESS;
    u0_m0_wo0_mtree_add0_12_q <= u0_m0_wo0_mtree_add0_12_o(14 downto 0);


	--u0_m0_wo0_mtree_add1_6(ADD,156)@13
    u0_m0_wo0_mtree_add1_6_a <= STD_LOGIC_VECTOR((16 downto 15 => u0_m0_wo0_mtree_add0_12_q(14)) & u0_m0_wo0_mtree_add0_12_q);
    u0_m0_wo0_mtree_add1_6_b <= STD_LOGIC_VECTOR((16 downto 16 => u0_m0_wo0_mtree_add0_13_q(15)) & u0_m0_wo0_mtree_add0_13_q);
    u0_m0_wo0_mtree_add1_6: PROCESS (clk, areset)
    BEGIN
        IF (areset = '1') THEN
            u0_m0_wo0_mtree_add1_6_o <= (others => '0');
        ELSIF(clk'EVENT AND clk = '1') THEN
            u0_m0_wo0_mtree_add1_6_o <= STD_LOGIC_VECTOR(SIGNED(u0_m0_wo0_mtree_add1_6_a) + SIGNED(u0_m0_wo0_mtree_add1_6_b));
        END IF;
    END PROCESS;
    u0_m0_wo0_mtree_add1_6_q <= u0_m0_wo0_mtree_add1_6_o(16 downto 0);


	--u0_m0_wo0_mtree_add2_3(ADD,163)@14
    u0_m0_wo0_mtree_add2_3_a <= STD_LOGIC_VECTOR((17 downto 17 => u0_m0_wo0_mtree_add1_6_q(16)) & u0_m0_wo0_mtree_add1_6_q);
    u0_m0_wo0_mtree_add2_3_b <= STD_LOGIC_VECTOR((17 downto 16 => u0_m0_wo0_mtree_add1_7_q(15)) & u0_m0_wo0_mtree_add1_7_q);
    u0_m0_wo0_mtree_add2_3: PROCESS (clk, areset)
    BEGIN
        IF (areset = '1') THEN
            u0_m0_wo0_mtree_add2_3_o <= (others => '0');
        ELSIF(clk'EVENT AND clk = '1') THEN
            u0_m0_wo0_mtree_add2_3_o <= STD_LOGIC_VECTOR(SIGNED(u0_m0_wo0_mtree_add2_3_a) + SIGNED(u0_m0_wo0_mtree_add2_3_b));
        END IF;
    END PROCESS;
    u0_m0_wo0_mtree_add2_3_q <= u0_m0_wo0_mtree_add2_3_o(17 downto 0);


	--u0_m0_wo0_mtree_mult1_23_shift0(BITSHIFT,227)@10
    u0_m0_wo0_mtree_mult1_23_shift0_q_int <= u0_m0_wo0_wi0_delayr17_q & "0000";
    u0_m0_wo0_mtree_mult1_23_shift0_q <= u0_m0_wo0_mtree_mult1_23_shift0_q_int(10 downto 0);

	--u0_m0_wo0_wi0_delayr17(DELAY,24)@10
    u0_m0_wo0_wi0_delayr17 : dspba_delay
    GENERIC MAP ( width => 7, depth => 1 )
    PORT MAP ( xin => u0_m0_wo0_wi0_delayr16_q, xout => u0_m0_wo0_wi0_delayr17_q, ena => xIn_v(0), clk => clk, aclr => areset );

	--u0_m0_wo0_mtree_mult1_23_add_1(ADD,228)@10
    u0_m0_wo0_mtree_mult1_23_add_1_a <= STD_LOGIC_VECTOR((11 downto 7 => u0_m0_wo0_wi0_delayr17_q(6)) & u0_m0_wo0_wi0_delayr17_q);
    u0_m0_wo0_mtree_mult1_23_add_1_b <= STD_LOGIC_VECTOR((11 downto 11 => u0_m0_wo0_mtree_mult1_23_shift0_q(10)) & u0_m0_wo0_mtree_mult1_23_shift0_q);
    u0_m0_wo0_mtree_mult1_23_add_1: PROCESS (clk, areset)
    BEGIN
        IF (areset = '1') THEN
            u0_m0_wo0_mtree_mult1_23_add_1_o <= (others => '0');
        ELSIF(clk'EVENT AND clk = '1') THEN
            u0_m0_wo0_mtree_mult1_23_add_1_o <= STD_LOGIC_VECTOR(SIGNED(u0_m0_wo0_mtree_mult1_23_add_1_a) + SIGNED(u0_m0_wo0_mtree_mult1_23_add_1_b));
        END IF;
    END PROCESS;
    u0_m0_wo0_mtree_mult1_23_add_1_q <= u0_m0_wo0_mtree_mult1_23_add_1_o(11 downto 0);


	--d_u0_m0_wo0_wi0_delayr17_q_11(DELAY,309)@10
    d_u0_m0_wo0_wi0_delayr17_q_11 : dspba_delay
    GENERIC MAP ( width => 7, depth => 1 )
    PORT MAP ( xin => u0_m0_wo0_wi0_delayr17_q, xout => d_u0_m0_wo0_wi0_delayr17_q_11_q, clk => clk, aclr => areset );

	--u0_m0_wo0_mtree_mult1_23_shift2(BITSHIFT,229)@11
    u0_m0_wo0_mtree_mult1_23_shift2_q_int <= d_u0_m0_wo0_wi0_delayr17_q_11_q & "0000000";
    u0_m0_wo0_mtree_mult1_23_shift2_q <= u0_m0_wo0_mtree_mult1_23_shift2_q_int(13 downto 0);

	--u0_m0_wo0_mtree_mult1_23_sub_3(SUB,230)@11
    u0_m0_wo0_mtree_mult1_23_sub_3_a <= STD_LOGIC_VECTOR((14 downto 14 => u0_m0_wo0_mtree_mult1_23_shift2_q(13)) & u0_m0_wo0_mtree_mult1_23_shift2_q);
    u0_m0_wo0_mtree_mult1_23_sub_3_b <= STD_LOGIC_VECTOR((14 downto 12 => u0_m0_wo0_mtree_mult1_23_add_1_q(11)) & u0_m0_wo0_mtree_mult1_23_add_1_q);
    u0_m0_wo0_mtree_mult1_23_sub_3: PROCESS (clk, areset)
    BEGIN
        IF (areset = '1') THEN
            u0_m0_wo0_mtree_mult1_23_sub_3_o <= (others => '0');
        ELSIF(clk'EVENT AND clk = '1') THEN
            u0_m0_wo0_mtree_mult1_23_sub_3_o <= STD_LOGIC_VECTOR(SIGNED(u0_m0_wo0_mtree_mult1_23_sub_3_a) - SIGNED(u0_m0_wo0_mtree_mult1_23_sub_3_b));
        END IF;
    END PROCESS;
    u0_m0_wo0_mtree_mult1_23_sub_3_q <= u0_m0_wo0_mtree_mult1_23_sub_3_o(14 downto 0);


	--u0_m0_wo0_mtree_mult1_22_shift0(BITSHIFT,231)@10
    u0_m0_wo0_mtree_mult1_22_shift0_q_int <= u0_m0_wo0_wi0_delayr18_q & "000";
    u0_m0_wo0_mtree_mult1_22_shift0_q <= u0_m0_wo0_mtree_mult1_22_shift0_q_int(9 downto 0);

	--u0_m0_wo0_wi0_delayr18(DELAY,25)@10
    u0_m0_wo0_wi0_delayr18 : dspba_delay
    GENERIC MAP ( width => 7, depth => 1 )
    PORT MAP ( xin => u0_m0_wo0_wi0_delayr17_q, xout => u0_m0_wo0_wi0_delayr18_q, ena => xIn_v(0), clk => clk, aclr => areset );

	--u0_m0_wo0_mtree_mult1_22_add_1(ADD,232)@10
    u0_m0_wo0_mtree_mult1_22_add_1_a <= STD_LOGIC_VECTOR((10 downto 7 => u0_m0_wo0_wi0_delayr18_q(6)) & u0_m0_wo0_wi0_delayr18_q);
    u0_m0_wo0_mtree_mult1_22_add_1_b <= STD_LOGIC_VECTOR((10 downto 10 => u0_m0_wo0_mtree_mult1_22_shift0_q(9)) & u0_m0_wo0_mtree_mult1_22_shift0_q);
    u0_m0_wo0_mtree_mult1_22_add_1: PROCESS (clk, areset)
    BEGIN
        IF (areset = '1') THEN
            u0_m0_wo0_mtree_mult1_22_add_1_o <= (others => '0');
        ELSIF(clk'EVENT AND clk = '1') THEN
            u0_m0_wo0_mtree_mult1_22_add_1_o <= STD_LOGIC_VECTOR(SIGNED(u0_m0_wo0_mtree_mult1_22_add_1_a) + SIGNED(u0_m0_wo0_mtree_mult1_22_add_1_b));
        END IF;
    END PROCESS;
    u0_m0_wo0_mtree_mult1_22_add_1_q <= u0_m0_wo0_mtree_mult1_22_add_1_o(10 downto 0);


	--d_u0_m0_wo0_wi0_delayr18_q_11(DELAY,310)@10
    d_u0_m0_wo0_wi0_delayr18_q_11 : dspba_delay
    GENERIC MAP ( width => 7, depth => 1 )
    PORT MAP ( xin => u0_m0_wo0_wi0_delayr18_q, xout => d_u0_m0_wo0_wi0_delayr18_q_11_q, clk => clk, aclr => areset );

	--u0_m0_wo0_mtree_mult1_22_shift2(BITSHIFT,233)@11
    u0_m0_wo0_mtree_mult1_22_shift2_q_int <= d_u0_m0_wo0_wi0_delayr18_q_11_q & "0000000";
    u0_m0_wo0_mtree_mult1_22_shift2_q <= u0_m0_wo0_mtree_mult1_22_shift2_q_int(13 downto 0);

	--u0_m0_wo0_mtree_mult1_22_sub_3(SUB,234)@11
    u0_m0_wo0_mtree_mult1_22_sub_3_a <= STD_LOGIC_VECTOR((14 downto 14 => u0_m0_wo0_mtree_mult1_22_shift2_q(13)) & u0_m0_wo0_mtree_mult1_22_shift2_q);
    u0_m0_wo0_mtree_mult1_22_sub_3_b <= STD_LOGIC_VECTOR((14 downto 11 => u0_m0_wo0_mtree_mult1_22_add_1_q(10)) & u0_m0_wo0_mtree_mult1_22_add_1_q);
    u0_m0_wo0_mtree_mult1_22_sub_3: PROCESS (clk, areset)
    BEGIN
        IF (areset = '1') THEN
            u0_m0_wo0_mtree_mult1_22_sub_3_o <= (others => '0');
        ELSIF(clk'EVENT AND clk = '1') THEN
            u0_m0_wo0_mtree_mult1_22_sub_3_o <= STD_LOGIC_VECTOR(SIGNED(u0_m0_wo0_mtree_mult1_22_sub_3_a) - SIGNED(u0_m0_wo0_mtree_mult1_22_sub_3_b));
        END IF;
    END PROCESS;
    u0_m0_wo0_mtree_mult1_22_sub_3_q <= u0_m0_wo0_mtree_mult1_22_sub_3_o(14 downto 0);


	--u0_m0_wo0_mtree_add0_11(ADD,141)@12
    u0_m0_wo0_mtree_add0_11_a <= STD_LOGIC_VECTOR((15 downto 15 => u0_m0_wo0_mtree_mult1_22_sub_3_q(14)) & u0_m0_wo0_mtree_mult1_22_sub_3_q);
    u0_m0_wo0_mtree_add0_11_b <= STD_LOGIC_VECTOR((15 downto 15 => u0_m0_wo0_mtree_mult1_23_sub_3_q(14)) & u0_m0_wo0_mtree_mult1_23_sub_3_q);
    u0_m0_wo0_mtree_add0_11: PROCESS (clk, areset)
    BEGIN
        IF (areset = '1') THEN
            u0_m0_wo0_mtree_add0_11_o <= (others => '0');
        ELSIF(clk'EVENT AND clk = '1') THEN
            u0_m0_wo0_mtree_add0_11_o <= STD_LOGIC_VECTOR(SIGNED(u0_m0_wo0_mtree_add0_11_a) + SIGNED(u0_m0_wo0_mtree_add0_11_b));
        END IF;
    END PROCESS;
    u0_m0_wo0_mtree_add0_11_q <= u0_m0_wo0_mtree_add0_11_o(15 downto 0);


	--u0_m0_wo0_wi0_delayr19(DELAY,26)@10
    u0_m0_wo0_wi0_delayr19 : dspba_delay
    GENERIC MAP ( width => 7, depth => 1 )
    PORT MAP ( xin => u0_m0_wo0_wi0_delayr18_q, xout => u0_m0_wo0_wi0_delayr19_q, ena => xIn_v(0), clk => clk, aclr => areset );

	--d_u0_m0_wo0_wi0_delayr19_q_11(DELAY,311)@10
    d_u0_m0_wo0_wi0_delayr19_q_11 : dspba_delay
    GENERIC MAP ( width => 7, depth => 1 )
    PORT MAP ( xin => u0_m0_wo0_wi0_delayr19_q, xout => d_u0_m0_wo0_wi0_delayr19_q_11_q, clk => clk, aclr => areset );

	--u0_m0_wo0_mtree_mult1_21_shift2(BITSHIFT,237)@11
    u0_m0_wo0_mtree_mult1_21_shift2_q_int <= d_u0_m0_wo0_wi0_delayr19_q_11_q & "0000000";
    u0_m0_wo0_mtree_mult1_21_shift2_q <= u0_m0_wo0_mtree_mult1_21_shift2_q_int(13 downto 0);

	--u0_m0_wo0_mtree_mult1_21_shift0(BITSHIFT,235)@10
    u0_m0_wo0_mtree_mult1_21_shift0_q_int <= u0_m0_wo0_wi0_delayr19_q & "00";
    u0_m0_wo0_mtree_mult1_21_shift0_q <= u0_m0_wo0_mtree_mult1_21_shift0_q_int(8 downto 0);

	--u0_m0_wo0_mtree_mult1_21_sub_1(SUB,236)@10
    u0_m0_wo0_mtree_mult1_21_sub_1_a <= STD_LOGIC_VECTOR((9 downto 7 => u0_m0_wo0_wi0_delayr19_q(6)) & u0_m0_wo0_wi0_delayr19_q);
    u0_m0_wo0_mtree_mult1_21_sub_1_b <= STD_LOGIC_VECTOR((9 downto 9 => u0_m0_wo0_mtree_mult1_21_shift0_q(8)) & u0_m0_wo0_mtree_mult1_21_shift0_q);
    u0_m0_wo0_mtree_mult1_21_sub_1: PROCESS (clk, areset)
    BEGIN
        IF (areset = '1') THEN
            u0_m0_wo0_mtree_mult1_21_sub_1_o <= (others => '0');
        ELSIF(clk'EVENT AND clk = '1') THEN
            u0_m0_wo0_mtree_mult1_21_sub_1_o <= STD_LOGIC_VECTOR(SIGNED(u0_m0_wo0_mtree_mult1_21_sub_1_a) - SIGNED(u0_m0_wo0_mtree_mult1_21_sub_1_b));
        END IF;
    END PROCESS;
    u0_m0_wo0_mtree_mult1_21_sub_1_q <= u0_m0_wo0_mtree_mult1_21_sub_1_o(9 downto 0);


	--u0_m0_wo0_mtree_mult1_21_add_3(ADD,238)@11
    u0_m0_wo0_mtree_mult1_21_add_3_a <= STD_LOGIC_VECTOR((14 downto 10 => u0_m0_wo0_mtree_mult1_21_sub_1_q(9)) & u0_m0_wo0_mtree_mult1_21_sub_1_q);
    u0_m0_wo0_mtree_mult1_21_add_3_b <= STD_LOGIC_VECTOR((14 downto 14 => u0_m0_wo0_mtree_mult1_21_shift2_q(13)) & u0_m0_wo0_mtree_mult1_21_shift2_q);
    u0_m0_wo0_mtree_mult1_21_add_3: PROCESS (clk, areset)
    BEGIN
        IF (areset = '1') THEN
            u0_m0_wo0_mtree_mult1_21_add_3_o <= (others => '0');
        ELSIF(clk'EVENT AND clk = '1') THEN
            u0_m0_wo0_mtree_mult1_21_add_3_o <= STD_LOGIC_VECTOR(SIGNED(u0_m0_wo0_mtree_mult1_21_add_3_a) + SIGNED(u0_m0_wo0_mtree_mult1_21_add_3_b));
        END IF;
    END PROCESS;
    u0_m0_wo0_mtree_mult1_21_add_3_q <= u0_m0_wo0_mtree_mult1_21_add_3_o(14 downto 0);


	--u0_m0_wo0_wi0_delayr20(DELAY,27)@10
    u0_m0_wo0_wi0_delayr20 : dspba_delay
    GENERIC MAP ( width => 7, depth => 1 )
    PORT MAP ( xin => u0_m0_wo0_wi0_delayr19_q, xout => u0_m0_wo0_wi0_delayr20_q, ena => xIn_v(0), clk => clk, aclr => areset );

	--d_u0_m0_wo0_wi0_delayr20_q_11(DELAY,312)@10
    d_u0_m0_wo0_wi0_delayr20_q_11 : dspba_delay
    GENERIC MAP ( width => 7, depth => 1 )
    PORT MAP ( xin => u0_m0_wo0_wi0_delayr20_q, xout => d_u0_m0_wo0_wi0_delayr20_q_11_q, clk => clk, aclr => areset );

	--u0_m0_wo0_mtree_mult1_20_shift0(BITSHIFT,239)@11
    u0_m0_wo0_mtree_mult1_20_shift0_q_int <= d_u0_m0_wo0_wi0_delayr20_q_11_q & "0000000";
    u0_m0_wo0_mtree_mult1_20_shift0_q <= u0_m0_wo0_mtree_mult1_20_shift0_q_int(13 downto 0);

	--u0_m0_wo0_mtree_mult1_20_sub_1(SUB,240)@11
    u0_m0_wo0_mtree_mult1_20_sub_1_a <= STD_LOGIC_VECTOR((14 downto 14 => u0_m0_wo0_mtree_mult1_20_shift0_q(13)) & u0_m0_wo0_mtree_mult1_20_shift0_q);
    u0_m0_wo0_mtree_mult1_20_sub_1_b <= STD_LOGIC_VECTOR((14 downto 7 => d_u0_m0_wo0_wi0_delayr20_q_11_q(6)) & d_u0_m0_wo0_wi0_delayr20_q_11_q);
    u0_m0_wo0_mtree_mult1_20_sub_1: PROCESS (clk, areset)
    BEGIN
        IF (areset = '1') THEN
            u0_m0_wo0_mtree_mult1_20_sub_1_o <= (others => '0');
        ELSIF(clk'EVENT AND clk = '1') THEN
            u0_m0_wo0_mtree_mult1_20_sub_1_o <= STD_LOGIC_VECTOR(SIGNED(u0_m0_wo0_mtree_mult1_20_sub_1_a) - SIGNED(u0_m0_wo0_mtree_mult1_20_sub_1_b));
        END IF;
    END PROCESS;
    u0_m0_wo0_mtree_mult1_20_sub_1_q <= u0_m0_wo0_mtree_mult1_20_sub_1_o(14 downto 0);


	--u0_m0_wo0_mtree_add0_10(ADD,140)@12
    u0_m0_wo0_mtree_add0_10_a <= STD_LOGIC_VECTOR((15 downto 15 => u0_m0_wo0_mtree_mult1_20_sub_1_q(14)) & u0_m0_wo0_mtree_mult1_20_sub_1_q);
    u0_m0_wo0_mtree_add0_10_b <= STD_LOGIC_VECTOR((15 downto 15 => u0_m0_wo0_mtree_mult1_21_add_3_q(14)) & u0_m0_wo0_mtree_mult1_21_add_3_q);
    u0_m0_wo0_mtree_add0_10: PROCESS (clk, areset)
    BEGIN
        IF (areset = '1') THEN
            u0_m0_wo0_mtree_add0_10_o <= (others => '0');
        ELSIF(clk'EVENT AND clk = '1') THEN
            u0_m0_wo0_mtree_add0_10_o <= STD_LOGIC_VECTOR(SIGNED(u0_m0_wo0_mtree_add0_10_a) + SIGNED(u0_m0_wo0_mtree_add0_10_b));
        END IF;
    END PROCESS;
    u0_m0_wo0_mtree_add0_10_q <= u0_m0_wo0_mtree_add0_10_o(15 downto 0);


	--u0_m0_wo0_mtree_add1_5(ADD,155)@13
    u0_m0_wo0_mtree_add1_5_a <= STD_LOGIC_VECTOR((16 downto 16 => u0_m0_wo0_mtree_add0_10_q(15)) & u0_m0_wo0_mtree_add0_10_q);
    u0_m0_wo0_mtree_add1_5_b <= STD_LOGIC_VECTOR((16 downto 16 => u0_m0_wo0_mtree_add0_11_q(15)) & u0_m0_wo0_mtree_add0_11_q);
    u0_m0_wo0_mtree_add1_5: PROCESS (clk, areset)
    BEGIN
        IF (areset = '1') THEN
            u0_m0_wo0_mtree_add1_5_o <= (others => '0');
        ELSIF(clk'EVENT AND clk = '1') THEN
            u0_m0_wo0_mtree_add1_5_o <= STD_LOGIC_VECTOR(SIGNED(u0_m0_wo0_mtree_add1_5_a) + SIGNED(u0_m0_wo0_mtree_add1_5_b));
        END IF;
    END PROCESS;
    u0_m0_wo0_mtree_add1_5_q <= u0_m0_wo0_mtree_add1_5_o(16 downto 0);


	--u0_m0_wo0_wi0_delayr21(DELAY,28)@10
    u0_m0_wo0_wi0_delayr21 : dspba_delay
    GENERIC MAP ( width => 7, depth => 1 )
    PORT MAP ( xin => u0_m0_wo0_wi0_delayr20_q, xout => u0_m0_wo0_wi0_delayr21_q, ena => xIn_v(0), clk => clk, aclr => areset );

	--d_u0_m0_wo0_wi0_delayr21_q_11(DELAY,313)@10
    d_u0_m0_wo0_wi0_delayr21_q_11 : dspba_delay
    GENERIC MAP ( width => 7, depth => 1 )
    PORT MAP ( xin => u0_m0_wo0_wi0_delayr21_q, xout => d_u0_m0_wo0_wi0_delayr21_q_11_q, clk => clk, aclr => areset );

	--u0_m0_wo0_mtree_mult1_19_shift2(BITSHIFT,243)@11
    u0_m0_wo0_mtree_mult1_19_shift2_q_int <= d_u0_m0_wo0_wi0_delayr21_q_11_q & "0000000";
    u0_m0_wo0_mtree_mult1_19_shift2_q <= u0_m0_wo0_mtree_mult1_19_shift2_q_int(13 downto 0);

	--u0_m0_wo0_mtree_mult1_19_shift0(BITSHIFT,241)@10
    u0_m0_wo0_mtree_mult1_19_shift0_q_int <= u0_m0_wo0_wi0_delayr21_q & "00";
    u0_m0_wo0_mtree_mult1_19_shift0_q <= u0_m0_wo0_mtree_mult1_19_shift0_q_int(8 downto 0);

	--u0_m0_wo0_mtree_mult1_19_sub_1(SUB,242)@10
    u0_m0_wo0_mtree_mult1_19_sub_1_a <= STD_LOGIC_VECTOR((9 downto 7 => u0_m0_wo0_wi0_delayr21_q(6)) & u0_m0_wo0_wi0_delayr21_q);
    u0_m0_wo0_mtree_mult1_19_sub_1_b <= STD_LOGIC_VECTOR((9 downto 9 => u0_m0_wo0_mtree_mult1_19_shift0_q(8)) & u0_m0_wo0_mtree_mult1_19_shift0_q);
    u0_m0_wo0_mtree_mult1_19_sub_1: PROCESS (clk, areset)
    BEGIN
        IF (areset = '1') THEN
            u0_m0_wo0_mtree_mult1_19_sub_1_o <= (others => '0');
        ELSIF(clk'EVENT AND clk = '1') THEN
            u0_m0_wo0_mtree_mult1_19_sub_1_o <= STD_LOGIC_VECTOR(SIGNED(u0_m0_wo0_mtree_mult1_19_sub_1_a) - SIGNED(u0_m0_wo0_mtree_mult1_19_sub_1_b));
        END IF;
    END PROCESS;
    u0_m0_wo0_mtree_mult1_19_sub_1_q <= u0_m0_wo0_mtree_mult1_19_sub_1_o(9 downto 0);


	--u0_m0_wo0_mtree_mult1_19_add_3(ADD,244)@11
    u0_m0_wo0_mtree_mult1_19_add_3_a <= STD_LOGIC_VECTOR((14 downto 10 => u0_m0_wo0_mtree_mult1_19_sub_1_q(9)) & u0_m0_wo0_mtree_mult1_19_sub_1_q);
    u0_m0_wo0_mtree_mult1_19_add_3_b <= STD_LOGIC_VECTOR((14 downto 14 => u0_m0_wo0_mtree_mult1_19_shift2_q(13)) & u0_m0_wo0_mtree_mult1_19_shift2_q);
    u0_m0_wo0_mtree_mult1_19_add_3: PROCESS (clk, areset)
    BEGIN
        IF (areset = '1') THEN
            u0_m0_wo0_mtree_mult1_19_add_3_o <= (others => '0');
        ELSIF(clk'EVENT AND clk = '1') THEN
            u0_m0_wo0_mtree_mult1_19_add_3_o <= STD_LOGIC_VECTOR(SIGNED(u0_m0_wo0_mtree_mult1_19_add_3_a) + SIGNED(u0_m0_wo0_mtree_mult1_19_add_3_b));
        END IF;
    END PROCESS;
    u0_m0_wo0_mtree_mult1_19_add_3_q <= u0_m0_wo0_mtree_mult1_19_add_3_o(14 downto 0);


	--u0_m0_wo0_mtree_mult1_18_shift0(BITSHIFT,245)@10
    u0_m0_wo0_mtree_mult1_18_shift0_q_int <= u0_m0_wo0_wi0_delayr22_q & "000";
    u0_m0_wo0_mtree_mult1_18_shift0_q <= u0_m0_wo0_mtree_mult1_18_shift0_q_int(9 downto 0);

	--u0_m0_wo0_wi0_delayr22(DELAY,29)@10
    u0_m0_wo0_wi0_delayr22 : dspba_delay
    GENERIC MAP ( width => 7, depth => 1 )
    PORT MAP ( xin => u0_m0_wo0_wi0_delayr21_q, xout => u0_m0_wo0_wi0_delayr22_q, ena => xIn_v(0), clk => clk, aclr => areset );

	--u0_m0_wo0_mtree_mult1_18_add_1(ADD,246)@10
    u0_m0_wo0_mtree_mult1_18_add_1_a <= STD_LOGIC_VECTOR((10 downto 7 => u0_m0_wo0_wi0_delayr22_q(6)) & u0_m0_wo0_wi0_delayr22_q);
    u0_m0_wo0_mtree_mult1_18_add_1_b <= STD_LOGIC_VECTOR((10 downto 10 => u0_m0_wo0_mtree_mult1_18_shift0_q(9)) & u0_m0_wo0_mtree_mult1_18_shift0_q);
    u0_m0_wo0_mtree_mult1_18_add_1: PROCESS (clk, areset)
    BEGIN
        IF (areset = '1') THEN
            u0_m0_wo0_mtree_mult1_18_add_1_o <= (others => '0');
        ELSIF(clk'EVENT AND clk = '1') THEN
            u0_m0_wo0_mtree_mult1_18_add_1_o <= STD_LOGIC_VECTOR(SIGNED(u0_m0_wo0_mtree_mult1_18_add_1_a) + SIGNED(u0_m0_wo0_mtree_mult1_18_add_1_b));
        END IF;
    END PROCESS;
    u0_m0_wo0_mtree_mult1_18_add_1_q <= u0_m0_wo0_mtree_mult1_18_add_1_o(10 downto 0);


	--d_u0_m0_wo0_wi0_delayr22_q_11(DELAY,314)@10
    d_u0_m0_wo0_wi0_delayr22_q_11 : dspba_delay
    GENERIC MAP ( width => 7, depth => 1 )
    PORT MAP ( xin => u0_m0_wo0_wi0_delayr22_q, xout => d_u0_m0_wo0_wi0_delayr22_q_11_q, clk => clk, aclr => areset );

	--u0_m0_wo0_mtree_mult1_18_shift2(BITSHIFT,247)@11
    u0_m0_wo0_mtree_mult1_18_shift2_q_int <= d_u0_m0_wo0_wi0_delayr22_q_11_q & "0000000";
    u0_m0_wo0_mtree_mult1_18_shift2_q <= u0_m0_wo0_mtree_mult1_18_shift2_q_int(13 downto 0);

	--u0_m0_wo0_mtree_mult1_18_sub_3(SUB,248)@11
    u0_m0_wo0_mtree_mult1_18_sub_3_a <= STD_LOGIC_VECTOR((14 downto 14 => u0_m0_wo0_mtree_mult1_18_shift2_q(13)) & u0_m0_wo0_mtree_mult1_18_shift2_q);
    u0_m0_wo0_mtree_mult1_18_sub_3_b <= STD_LOGIC_VECTOR((14 downto 11 => u0_m0_wo0_mtree_mult1_18_add_1_q(10)) & u0_m0_wo0_mtree_mult1_18_add_1_q);
    u0_m0_wo0_mtree_mult1_18_sub_3: PROCESS (clk, areset)
    BEGIN
        IF (areset = '1') THEN
            u0_m0_wo0_mtree_mult1_18_sub_3_o <= (others => '0');
        ELSIF(clk'EVENT AND clk = '1') THEN
            u0_m0_wo0_mtree_mult1_18_sub_3_o <= STD_LOGIC_VECTOR(SIGNED(u0_m0_wo0_mtree_mult1_18_sub_3_a) - SIGNED(u0_m0_wo0_mtree_mult1_18_sub_3_b));
        END IF;
    END PROCESS;
    u0_m0_wo0_mtree_mult1_18_sub_3_q <= u0_m0_wo0_mtree_mult1_18_sub_3_o(14 downto 0);


	--u0_m0_wo0_mtree_add0_9(ADD,139)@12
    u0_m0_wo0_mtree_add0_9_a <= STD_LOGIC_VECTOR((15 downto 15 => u0_m0_wo0_mtree_mult1_18_sub_3_q(14)) & u0_m0_wo0_mtree_mult1_18_sub_3_q);
    u0_m0_wo0_mtree_add0_9_b <= STD_LOGIC_VECTOR((15 downto 15 => u0_m0_wo0_mtree_mult1_19_add_3_q(14)) & u0_m0_wo0_mtree_mult1_19_add_3_q);
    u0_m0_wo0_mtree_add0_9: PROCESS (clk, areset)
    BEGIN
        IF (areset = '1') THEN
            u0_m0_wo0_mtree_add0_9_o <= (others => '0');
        ELSIF(clk'EVENT AND clk = '1') THEN
            u0_m0_wo0_mtree_add0_9_o <= STD_LOGIC_VECTOR(SIGNED(u0_m0_wo0_mtree_add0_9_a) + SIGNED(u0_m0_wo0_mtree_add0_9_b));
        END IF;
    END PROCESS;
    u0_m0_wo0_mtree_add0_9_q <= u0_m0_wo0_mtree_add0_9_o(15 downto 0);


	--u0_m0_wo0_mtree_mult1_17_shift0(BITSHIFT,249)@10
    u0_m0_wo0_mtree_mult1_17_shift0_q_int <= u0_m0_wo0_wi0_delayr23_q & "0000";
    u0_m0_wo0_mtree_mult1_17_shift0_q <= u0_m0_wo0_mtree_mult1_17_shift0_q_int(10 downto 0);

	--u0_m0_wo0_wi0_delayr23(DELAY,30)@10
    u0_m0_wo0_wi0_delayr23 : dspba_delay
    GENERIC MAP ( width => 7, depth => 1 )
    PORT MAP ( xin => u0_m0_wo0_wi0_delayr22_q, xout => u0_m0_wo0_wi0_delayr23_q, ena => xIn_v(0), clk => clk, aclr => areset );

	--u0_m0_wo0_mtree_mult1_17_add_1(ADD,250)@10
    u0_m0_wo0_mtree_mult1_17_add_1_a <= STD_LOGIC_VECTOR((11 downto 7 => u0_m0_wo0_wi0_delayr23_q(6)) & u0_m0_wo0_wi0_delayr23_q);
    u0_m0_wo0_mtree_mult1_17_add_1_b <= STD_LOGIC_VECTOR((11 downto 11 => u0_m0_wo0_mtree_mult1_17_shift0_q(10)) & u0_m0_wo0_mtree_mult1_17_shift0_q);
    u0_m0_wo0_mtree_mult1_17_add_1: PROCESS (clk, areset)
    BEGIN
        IF (areset = '1') THEN
            u0_m0_wo0_mtree_mult1_17_add_1_o <= (others => '0');
        ELSIF(clk'EVENT AND clk = '1') THEN
            u0_m0_wo0_mtree_mult1_17_add_1_o <= STD_LOGIC_VECTOR(SIGNED(u0_m0_wo0_mtree_mult1_17_add_1_a) + SIGNED(u0_m0_wo0_mtree_mult1_17_add_1_b));
        END IF;
    END PROCESS;
    u0_m0_wo0_mtree_mult1_17_add_1_q <= u0_m0_wo0_mtree_mult1_17_add_1_o(11 downto 0);


	--d_u0_m0_wo0_wi0_delayr23_q_11(DELAY,315)@10
    d_u0_m0_wo0_wi0_delayr23_q_11 : dspba_delay
    GENERIC MAP ( width => 7, depth => 1 )
    PORT MAP ( xin => u0_m0_wo0_wi0_delayr23_q, xout => d_u0_m0_wo0_wi0_delayr23_q_11_q, clk => clk, aclr => areset );

	--u0_m0_wo0_mtree_mult1_17_shift2(BITSHIFT,251)@11
    u0_m0_wo0_mtree_mult1_17_shift2_q_int <= d_u0_m0_wo0_wi0_delayr23_q_11_q & "0000000";
    u0_m0_wo0_mtree_mult1_17_shift2_q <= u0_m0_wo0_mtree_mult1_17_shift2_q_int(13 downto 0);

	--u0_m0_wo0_mtree_mult1_17_sub_3(SUB,252)@11
    u0_m0_wo0_mtree_mult1_17_sub_3_a <= STD_LOGIC_VECTOR((14 downto 14 => u0_m0_wo0_mtree_mult1_17_shift2_q(13)) & u0_m0_wo0_mtree_mult1_17_shift2_q);
    u0_m0_wo0_mtree_mult1_17_sub_3_b <= STD_LOGIC_VECTOR((14 downto 12 => u0_m0_wo0_mtree_mult1_17_add_1_q(11)) & u0_m0_wo0_mtree_mult1_17_add_1_q);
    u0_m0_wo0_mtree_mult1_17_sub_3: PROCESS (clk, areset)
    BEGIN
        IF (areset = '1') THEN
            u0_m0_wo0_mtree_mult1_17_sub_3_o <= (others => '0');
        ELSIF(clk'EVENT AND clk = '1') THEN
            u0_m0_wo0_mtree_mult1_17_sub_3_o <= STD_LOGIC_VECTOR(SIGNED(u0_m0_wo0_mtree_mult1_17_sub_3_a) - SIGNED(u0_m0_wo0_mtree_mult1_17_sub_3_b));
        END IF;
    END PROCESS;
    u0_m0_wo0_mtree_mult1_17_sub_3_q <= u0_m0_wo0_mtree_mult1_17_sub_3_o(14 downto 0);


	--u0_m0_wo0_wi0_delayr24(DELAY,31)@10
    u0_m0_wo0_wi0_delayr24 : dspba_delay
    GENERIC MAP ( width => 7, depth => 1 )
    PORT MAP ( xin => u0_m0_wo0_wi0_delayr23_q, xout => u0_m0_wo0_wi0_delayr24_q, ena => xIn_v(0), clk => clk, aclr => areset );

	--d_u0_m0_wo0_wi0_delayr24_q_11(DELAY,316)@10
    d_u0_m0_wo0_wi0_delayr24_q_11 : dspba_delay
    GENERIC MAP ( width => 7, depth => 1 )
    PORT MAP ( xin => u0_m0_wo0_wi0_delayr24_q, xout => d_u0_m0_wo0_wi0_delayr24_q_11_q, clk => clk, aclr => areset );

	--u0_m0_wo0_mtree_mult1_16_shift2(BITSHIFT,255)@11
    u0_m0_wo0_mtree_mult1_16_shift2_q_int <= d_u0_m0_wo0_wi0_delayr24_q_11_q & "0000";
    u0_m0_wo0_mtree_mult1_16_shift2_q <= u0_m0_wo0_mtree_mult1_16_shift2_q_int(10 downto 0);

	--u0_m0_wo0_mtree_mult1_16_shift0(BITSHIFT,253)@10
    u0_m0_wo0_mtree_mult1_16_shift0_q_int <= u0_m0_wo0_wi0_delayr24_q & "000";
    u0_m0_wo0_mtree_mult1_16_shift0_q <= u0_m0_wo0_mtree_mult1_16_shift0_q_int(9 downto 0);

	--u0_m0_wo0_mtree_mult1_16_add_1(ADD,254)@10
    u0_m0_wo0_mtree_mult1_16_add_1_a <= STD_LOGIC_VECTOR((10 downto 7 => u0_m0_wo0_wi0_delayr24_q(6)) & u0_m0_wo0_wi0_delayr24_q);
    u0_m0_wo0_mtree_mult1_16_add_1_b <= STD_LOGIC_VECTOR((10 downto 10 => u0_m0_wo0_mtree_mult1_16_shift0_q(9)) & u0_m0_wo0_mtree_mult1_16_shift0_q);
    u0_m0_wo0_mtree_mult1_16_add_1: PROCESS (clk, areset)
    BEGIN
        IF (areset = '1') THEN
            u0_m0_wo0_mtree_mult1_16_add_1_o <= (others => '0');
        ELSIF(clk'EVENT AND clk = '1') THEN
            u0_m0_wo0_mtree_mult1_16_add_1_o <= STD_LOGIC_VECTOR(SIGNED(u0_m0_wo0_mtree_mult1_16_add_1_a) + SIGNED(u0_m0_wo0_mtree_mult1_16_add_1_b));
        END IF;
    END PROCESS;
    u0_m0_wo0_mtree_mult1_16_add_1_q <= u0_m0_wo0_mtree_mult1_16_add_1_o(10 downto 0);


	--u0_m0_wo0_mtree_mult1_16_add_3(ADD,256)@11
    u0_m0_wo0_mtree_mult1_16_add_3_a <= STD_LOGIC_VECTOR((11 downto 11 => u0_m0_wo0_mtree_mult1_16_add_1_q(10)) & u0_m0_wo0_mtree_mult1_16_add_1_q);
    u0_m0_wo0_mtree_mult1_16_add_3_b <= STD_LOGIC_VECTOR((11 downto 11 => u0_m0_wo0_mtree_mult1_16_shift2_q(10)) & u0_m0_wo0_mtree_mult1_16_shift2_q);
    u0_m0_wo0_mtree_mult1_16_add_3: PROCESS (clk, areset)
    BEGIN
        IF (areset = '1') THEN
            u0_m0_wo0_mtree_mult1_16_add_3_o <= (others => '0');
        ELSIF(clk'EVENT AND clk = '1') THEN
            u0_m0_wo0_mtree_mult1_16_add_3_o <= STD_LOGIC_VECTOR(SIGNED(u0_m0_wo0_mtree_mult1_16_add_3_a) + SIGNED(u0_m0_wo0_mtree_mult1_16_add_3_b));
        END IF;
    END PROCESS;
    u0_m0_wo0_mtree_mult1_16_add_3_q <= u0_m0_wo0_mtree_mult1_16_add_3_o(11 downto 0);


	--u0_m0_wo0_mtree_mult1_16_shift4(BITSHIFT,257)@12
    u0_m0_wo0_mtree_mult1_16_shift4_q_int <= u0_m0_wo0_mtree_mult1_16_add_3_q & "00";
    u0_m0_wo0_mtree_mult1_16_shift4_q <= u0_m0_wo0_mtree_mult1_16_shift4_q_int(13 downto 0);

	--u0_m0_wo0_mtree_add0_8(ADD,138)@12
    u0_m0_wo0_mtree_add0_8_a <= STD_LOGIC_VECTOR((15 downto 14 => u0_m0_wo0_mtree_mult1_16_shift4_q(13)) & u0_m0_wo0_mtree_mult1_16_shift4_q);
    u0_m0_wo0_mtree_add0_8_b <= STD_LOGIC_VECTOR((15 downto 15 => u0_m0_wo0_mtree_mult1_17_sub_3_q(14)) & u0_m0_wo0_mtree_mult1_17_sub_3_q);
    u0_m0_wo0_mtree_add0_8: PROCESS (clk, areset)
    BEGIN
        IF (areset = '1') THEN
            u0_m0_wo0_mtree_add0_8_o <= (others => '0');
        ELSIF(clk'EVENT AND clk = '1') THEN
            u0_m0_wo0_mtree_add0_8_o <= STD_LOGIC_VECTOR(SIGNED(u0_m0_wo0_mtree_add0_8_a) + SIGNED(u0_m0_wo0_mtree_add0_8_b));
        END IF;
    END PROCESS;
    u0_m0_wo0_mtree_add0_8_q <= u0_m0_wo0_mtree_add0_8_o(15 downto 0);


	--u0_m0_wo0_mtree_add1_4(ADD,154)@13
    u0_m0_wo0_mtree_add1_4_a <= STD_LOGIC_VECTOR((16 downto 16 => u0_m0_wo0_mtree_add0_8_q(15)) & u0_m0_wo0_mtree_add0_8_q);
    u0_m0_wo0_mtree_add1_4_b <= STD_LOGIC_VECTOR((16 downto 16 => u0_m0_wo0_mtree_add0_9_q(15)) & u0_m0_wo0_mtree_add0_9_q);
    u0_m0_wo0_mtree_add1_4: PROCESS (clk, areset)
    BEGIN
        IF (areset = '1') THEN
            u0_m0_wo0_mtree_add1_4_o <= (others => '0');
        ELSIF(clk'EVENT AND clk = '1') THEN
            u0_m0_wo0_mtree_add1_4_o <= STD_LOGIC_VECTOR(SIGNED(u0_m0_wo0_mtree_add1_4_a) + SIGNED(u0_m0_wo0_mtree_add1_4_b));
        END IF;
    END PROCESS;
    u0_m0_wo0_mtree_add1_4_q <= u0_m0_wo0_mtree_add1_4_o(16 downto 0);


	--u0_m0_wo0_mtree_add2_2(ADD,162)@14
    u0_m0_wo0_mtree_add2_2_a <= STD_LOGIC_VECTOR((17 downto 17 => u0_m0_wo0_mtree_add1_4_q(16)) & u0_m0_wo0_mtree_add1_4_q);
    u0_m0_wo0_mtree_add2_2_b <= STD_LOGIC_VECTOR((17 downto 17 => u0_m0_wo0_mtree_add1_5_q(16)) & u0_m0_wo0_mtree_add1_5_q);
    u0_m0_wo0_mtree_add2_2: PROCESS (clk, areset)
    BEGIN
        IF (areset = '1') THEN
            u0_m0_wo0_mtree_add2_2_o <= (others => '0');
        ELSIF(clk'EVENT AND clk = '1') THEN
            u0_m0_wo0_mtree_add2_2_o <= STD_LOGIC_VECTOR(SIGNED(u0_m0_wo0_mtree_add2_2_a) + SIGNED(u0_m0_wo0_mtree_add2_2_b));
        END IF;
    END PROCESS;
    u0_m0_wo0_mtree_add2_2_q <= u0_m0_wo0_mtree_add2_2_o(17 downto 0);


	--u0_m0_wo0_mtree_add3_1(ADD,166)@15
    u0_m0_wo0_mtree_add3_1_a <= STD_LOGIC_VECTOR((18 downto 18 => u0_m0_wo0_mtree_add2_2_q(17)) & u0_m0_wo0_mtree_add2_2_q);
    u0_m0_wo0_mtree_add3_1_b <= STD_LOGIC_VECTOR((18 downto 18 => u0_m0_wo0_mtree_add2_3_q(17)) & u0_m0_wo0_mtree_add2_3_q);
    u0_m0_wo0_mtree_add3_1: PROCESS (clk, areset)
    BEGIN
        IF (areset = '1') THEN
            u0_m0_wo0_mtree_add3_1_o <= (others => '0');
        ELSIF(clk'EVENT AND clk = '1') THEN
            u0_m0_wo0_mtree_add3_1_o <= STD_LOGIC_VECTOR(SIGNED(u0_m0_wo0_mtree_add3_1_a) + SIGNED(u0_m0_wo0_mtree_add3_1_b));
        END IF;
    END PROCESS;
    u0_m0_wo0_mtree_add3_1_q <= u0_m0_wo0_mtree_add3_1_o(18 downto 0);


	--u0_m0_wo0_wi0_delayr25(DELAY,32)@10
    u0_m0_wo0_wi0_delayr25 : dspba_delay
    GENERIC MAP ( width => 7, depth => 1 )
    PORT MAP ( xin => u0_m0_wo0_wi0_delayr24_q, xout => u0_m0_wo0_wi0_delayr25_q, ena => xIn_v(0), clk => clk, aclr => areset );

	--d_u0_m0_wo0_wi0_delayr25_q_11(DELAY,317)@10
    d_u0_m0_wo0_wi0_delayr25_q_11 : dspba_delay
    GENERIC MAP ( width => 7, depth => 1 )
    PORT MAP ( xin => u0_m0_wo0_wi0_delayr25_q, xout => d_u0_m0_wo0_wi0_delayr25_q_11_q, clk => clk, aclr => areset );

	--u0_m0_wo0_mtree_mult1_15_shift2(BITSHIFT,260)@11
    u0_m0_wo0_mtree_mult1_15_shift2_q_int <= d_u0_m0_wo0_wi0_delayr25_q_11_q & "000";
    u0_m0_wo0_mtree_mult1_15_shift2_q <= u0_m0_wo0_mtree_mult1_15_shift2_q_int(9 downto 0);

	--u0_m0_wo0_mtree_mult1_15_shift0(BITSHIFT,258)@10
    u0_m0_wo0_mtree_mult1_15_shift0_q_int <= u0_m0_wo0_wi0_delayr25_q & "0";
    u0_m0_wo0_mtree_mult1_15_shift0_q <= u0_m0_wo0_mtree_mult1_15_shift0_q_int(7 downto 0);

	--u0_m0_wo0_mtree_mult1_15_add_1(ADD,259)@10
    u0_m0_wo0_mtree_mult1_15_add_1_a <= STD_LOGIC_VECTOR((8 downto 7 => u0_m0_wo0_wi0_delayr25_q(6)) & u0_m0_wo0_wi0_delayr25_q);
    u0_m0_wo0_mtree_mult1_15_add_1_b <= STD_LOGIC_VECTOR((8 downto 8 => u0_m0_wo0_mtree_mult1_15_shift0_q(7)) & u0_m0_wo0_mtree_mult1_15_shift0_q);
    u0_m0_wo0_mtree_mult1_15_add_1: PROCESS (clk, areset)
    BEGIN
        IF (areset = '1') THEN
            u0_m0_wo0_mtree_mult1_15_add_1_o <= (others => '0');
        ELSIF(clk'EVENT AND clk = '1') THEN
            u0_m0_wo0_mtree_mult1_15_add_1_o <= STD_LOGIC_VECTOR(SIGNED(u0_m0_wo0_mtree_mult1_15_add_1_a) + SIGNED(u0_m0_wo0_mtree_mult1_15_add_1_b));
        END IF;
    END PROCESS;
    u0_m0_wo0_mtree_mult1_15_add_1_q <= u0_m0_wo0_mtree_mult1_15_add_1_o(8 downto 0);


	--u0_m0_wo0_mtree_mult1_15_add_3(ADD,261)@11
    u0_m0_wo0_mtree_mult1_15_add_3_a <= STD_LOGIC_VECTOR((10 downto 9 => u0_m0_wo0_mtree_mult1_15_add_1_q(8)) & u0_m0_wo0_mtree_mult1_15_add_1_q);
    u0_m0_wo0_mtree_mult1_15_add_3_b <= STD_LOGIC_VECTOR((10 downto 10 => u0_m0_wo0_mtree_mult1_15_shift2_q(9)) & u0_m0_wo0_mtree_mult1_15_shift2_q);
    u0_m0_wo0_mtree_mult1_15_add_3: PROCESS (clk, areset)
    BEGIN
        IF (areset = '1') THEN
            u0_m0_wo0_mtree_mult1_15_add_3_o <= (others => '0');
        ELSIF(clk'EVENT AND clk = '1') THEN
            u0_m0_wo0_mtree_mult1_15_add_3_o <= STD_LOGIC_VECTOR(SIGNED(u0_m0_wo0_mtree_mult1_15_add_3_a) + SIGNED(u0_m0_wo0_mtree_mult1_15_add_3_b));
        END IF;
    END PROCESS;
    u0_m0_wo0_mtree_mult1_15_add_3_q <= u0_m0_wo0_mtree_mult1_15_add_3_o(10 downto 0);


	--u0_m0_wo0_mtree_mult1_15_shift4(BITSHIFT,262)@12
    u0_m0_wo0_mtree_mult1_15_shift4_q_int <= u0_m0_wo0_mtree_mult1_15_add_3_q & "000";
    u0_m0_wo0_mtree_mult1_15_shift4_q <= u0_m0_wo0_mtree_mult1_15_shift4_q_int(13 downto 0);

	--u0_m0_wo0_mtree_mult1_14_shift2(BITSHIFT,265)@10
    u0_m0_wo0_mtree_mult1_14_shift2_q_int <= u0_m0_wo0_wi0_delayr26_q & "000";
    u0_m0_wo0_mtree_mult1_14_shift2_q <= u0_m0_wo0_mtree_mult1_14_shift2_q_int(9 downto 0);

	--u0_m0_wo0_wi0_delayr26(DELAY,33)@10
    u0_m0_wo0_wi0_delayr26 : dspba_delay
    GENERIC MAP ( width => 7, depth => 1 )
    PORT MAP ( xin => u0_m0_wo0_wi0_delayr25_q, xout => u0_m0_wo0_wi0_delayr26_q, ena => xIn_v(0), clk => clk, aclr => areset );

	--u0_m0_wo0_mtree_mult1_14_add_3(ADD,266)@10
    u0_m0_wo0_mtree_mult1_14_add_3_a <= STD_LOGIC_VECTOR((10 downto 7 => u0_m0_wo0_wi0_delayr26_q(6)) & u0_m0_wo0_wi0_delayr26_q);
    u0_m0_wo0_mtree_mult1_14_add_3_b <= STD_LOGIC_VECTOR((10 downto 10 => u0_m0_wo0_mtree_mult1_14_shift2_q(9)) & u0_m0_wo0_mtree_mult1_14_shift2_q);
    u0_m0_wo0_mtree_mult1_14_add_3: PROCESS (clk, areset)
    BEGIN
        IF (areset = '1') THEN
            u0_m0_wo0_mtree_mult1_14_add_3_o <= (others => '0');
        ELSIF(clk'EVENT AND clk = '1') THEN
            u0_m0_wo0_mtree_mult1_14_add_3_o <= STD_LOGIC_VECTOR(SIGNED(u0_m0_wo0_mtree_mult1_14_add_3_a) + SIGNED(u0_m0_wo0_mtree_mult1_14_add_3_b));
        END IF;
    END PROCESS;
    u0_m0_wo0_mtree_mult1_14_add_3_q <= u0_m0_wo0_mtree_mult1_14_add_3_o(10 downto 0);


	--u0_m0_wo0_mtree_mult1_14_shift4(BITSHIFT,267)@11
    u0_m0_wo0_mtree_mult1_14_shift4_q_int <= u0_m0_wo0_mtree_mult1_14_add_3_q & "000";
    u0_m0_wo0_mtree_mult1_14_shift4_q <= u0_m0_wo0_mtree_mult1_14_shift4_q_int(13 downto 0);

	--u0_m0_wo0_mtree_mult1_14_shift0(BITSHIFT,263)@10
    u0_m0_wo0_mtree_mult1_14_shift0_q_int <= u0_m0_wo0_wi0_delayr26_q & "0";
    u0_m0_wo0_mtree_mult1_14_shift0_q <= u0_m0_wo0_mtree_mult1_14_shift0_q_int(7 downto 0);

	--u0_m0_wo0_mtree_mult1_14_add_1(ADD,264)@10
    u0_m0_wo0_mtree_mult1_14_add_1_a <= STD_LOGIC_VECTOR((8 downto 7 => u0_m0_wo0_wi0_delayr26_q(6)) & u0_m0_wo0_wi0_delayr26_q);
    u0_m0_wo0_mtree_mult1_14_add_1_b <= STD_LOGIC_VECTOR((8 downto 8 => u0_m0_wo0_mtree_mult1_14_shift0_q(7)) & u0_m0_wo0_mtree_mult1_14_shift0_q);
    u0_m0_wo0_mtree_mult1_14_add_1: PROCESS (clk, areset)
    BEGIN
        IF (areset = '1') THEN
            u0_m0_wo0_mtree_mult1_14_add_1_o <= (others => '0');
        ELSIF(clk'EVENT AND clk = '1') THEN
            u0_m0_wo0_mtree_mult1_14_add_1_o <= STD_LOGIC_VECTOR(SIGNED(u0_m0_wo0_mtree_mult1_14_add_1_a) + SIGNED(u0_m0_wo0_mtree_mult1_14_add_1_b));
        END IF;
    END PROCESS;
    u0_m0_wo0_mtree_mult1_14_add_1_q <= u0_m0_wo0_mtree_mult1_14_add_1_o(8 downto 0);


	--u0_m0_wo0_mtree_mult1_14_add_5(ADD,268)@11
    u0_m0_wo0_mtree_mult1_14_add_5_a <= STD_LOGIC_VECTOR((14 downto 9 => u0_m0_wo0_mtree_mult1_14_add_1_q(8)) & u0_m0_wo0_mtree_mult1_14_add_1_q);
    u0_m0_wo0_mtree_mult1_14_add_5_b <= STD_LOGIC_VECTOR((14 downto 14 => u0_m0_wo0_mtree_mult1_14_shift4_q(13)) & u0_m0_wo0_mtree_mult1_14_shift4_q);
    u0_m0_wo0_mtree_mult1_14_add_5: PROCESS (clk, areset)
    BEGIN
        IF (areset = '1') THEN
            u0_m0_wo0_mtree_mult1_14_add_5_o <= (others => '0');
        ELSIF(clk'EVENT AND clk = '1') THEN
            u0_m0_wo0_mtree_mult1_14_add_5_o <= STD_LOGIC_VECTOR(SIGNED(u0_m0_wo0_mtree_mult1_14_add_5_a) + SIGNED(u0_m0_wo0_mtree_mult1_14_add_5_b));
        END IF;
    END PROCESS;
    u0_m0_wo0_mtree_mult1_14_add_5_q <= u0_m0_wo0_mtree_mult1_14_add_5_o(14 downto 0);


	--u0_m0_wo0_mtree_add0_7(ADD,137)@12
    u0_m0_wo0_mtree_add0_7_a <= STD_LOGIC_VECTOR((15 downto 15 => u0_m0_wo0_mtree_mult1_14_add_5_q(14)) & u0_m0_wo0_mtree_mult1_14_add_5_q);
    u0_m0_wo0_mtree_add0_7_b <= STD_LOGIC_VECTOR((15 downto 14 => u0_m0_wo0_mtree_mult1_15_shift4_q(13)) & u0_m0_wo0_mtree_mult1_15_shift4_q);
    u0_m0_wo0_mtree_add0_7: PROCESS (clk, areset)
    BEGIN
        IF (areset = '1') THEN
            u0_m0_wo0_mtree_add0_7_o <= (others => '0');
        ELSIF(clk'EVENT AND clk = '1') THEN
            u0_m0_wo0_mtree_add0_7_o <= STD_LOGIC_VECTOR(SIGNED(u0_m0_wo0_mtree_add0_7_a) + SIGNED(u0_m0_wo0_mtree_add0_7_b));
        END IF;
    END PROCESS;
    u0_m0_wo0_mtree_add0_7_q <= u0_m0_wo0_mtree_add0_7_o(15 downto 0);


	--u0_m0_wo0_wi0_delayr27(DELAY,34)@10
    u0_m0_wo0_wi0_delayr27 : dspba_delay
    GENERIC MAP ( width => 7, depth => 1 )
    PORT MAP ( xin => u0_m0_wo0_wi0_delayr26_q, xout => u0_m0_wo0_wi0_delayr27_q, ena => xIn_v(0), clk => clk, aclr => areset );

	--d_u0_m0_wo0_wi0_delayr27_q_11(DELAY,318)@10
    d_u0_m0_wo0_wi0_delayr27_q_11 : dspba_delay
    GENERIC MAP ( width => 7, depth => 1 )
    PORT MAP ( xin => u0_m0_wo0_wi0_delayr27_q, xout => d_u0_m0_wo0_wi0_delayr27_q_11_q, clk => clk, aclr => areset );

	--u0_m0_wo0_mtree_mult1_13_shift2(BITSHIFT,271)@11
    u0_m0_wo0_mtree_mult1_13_shift2_q_int <= d_u0_m0_wo0_wi0_delayr27_q_11_q & "000000";
    u0_m0_wo0_mtree_mult1_13_shift2_q <= u0_m0_wo0_mtree_mult1_13_shift2_q_int(12 downto 0);

	--u0_m0_wo0_mtree_mult1_13_shift0(BITSHIFT,269)@10
    u0_m0_wo0_mtree_mult1_13_shift0_q_int <= u0_m0_wo0_wi0_delayr27_q & "00";
    u0_m0_wo0_mtree_mult1_13_shift0_q <= u0_m0_wo0_mtree_mult1_13_shift0_q_int(8 downto 0);

	--u0_m0_wo0_mtree_mult1_13_sub_1(SUB,270)@10
    u0_m0_wo0_mtree_mult1_13_sub_1_a <= STD_LOGIC_VECTOR((9 downto 7 => u0_m0_wo0_wi0_delayr27_q(6)) & u0_m0_wo0_wi0_delayr27_q);
    u0_m0_wo0_mtree_mult1_13_sub_1_b <= STD_LOGIC_VECTOR((9 downto 9 => u0_m0_wo0_mtree_mult1_13_shift0_q(8)) & u0_m0_wo0_mtree_mult1_13_shift0_q);
    u0_m0_wo0_mtree_mult1_13_sub_1: PROCESS (clk, areset)
    BEGIN
        IF (areset = '1') THEN
            u0_m0_wo0_mtree_mult1_13_sub_1_o <= (others => '0');
        ELSIF(clk'EVENT AND clk = '1') THEN
            u0_m0_wo0_mtree_mult1_13_sub_1_o <= STD_LOGIC_VECTOR(SIGNED(u0_m0_wo0_mtree_mult1_13_sub_1_a) - SIGNED(u0_m0_wo0_mtree_mult1_13_sub_1_b));
        END IF;
    END PROCESS;
    u0_m0_wo0_mtree_mult1_13_sub_1_q <= u0_m0_wo0_mtree_mult1_13_sub_1_o(9 downto 0);


	--u0_m0_wo0_mtree_mult1_13_add_3(ADD,272)@11
    u0_m0_wo0_mtree_mult1_13_add_3_a <= STD_LOGIC_VECTOR((13 downto 10 => u0_m0_wo0_mtree_mult1_13_sub_1_q(9)) & u0_m0_wo0_mtree_mult1_13_sub_1_q);
    u0_m0_wo0_mtree_mult1_13_add_3_b <= STD_LOGIC_VECTOR((13 downto 13 => u0_m0_wo0_mtree_mult1_13_shift2_q(12)) & u0_m0_wo0_mtree_mult1_13_shift2_q);
    u0_m0_wo0_mtree_mult1_13_add_3: PROCESS (clk, areset)
    BEGIN
        IF (areset = '1') THEN
            u0_m0_wo0_mtree_mult1_13_add_3_o <= (others => '0');
        ELSIF(clk'EVENT AND clk = '1') THEN
            u0_m0_wo0_mtree_mult1_13_add_3_o <= STD_LOGIC_VECTOR(SIGNED(u0_m0_wo0_mtree_mult1_13_add_3_a) + SIGNED(u0_m0_wo0_mtree_mult1_13_add_3_b));
        END IF;
    END PROCESS;
    u0_m0_wo0_mtree_mult1_13_add_3_q <= u0_m0_wo0_mtree_mult1_13_add_3_o(13 downto 0);


	--u0_m0_wo0_mtree_mult1_12_shift0(BITSHIFT,273)@11
    u0_m0_wo0_mtree_mult1_12_shift0_q_int <= d_u0_m0_wo0_wi0_delayr28_q_11_q & "0";
    u0_m0_wo0_mtree_mult1_12_shift0_q <= u0_m0_wo0_mtree_mult1_12_shift0_q_int(7 downto 0);

	--u0_m0_wo0_wi0_delayr28(DELAY,35)@10
    u0_m0_wo0_wi0_delayr28 : dspba_delay
    GENERIC MAP ( width => 7, depth => 1 )
    PORT MAP ( xin => u0_m0_wo0_wi0_delayr27_q, xout => u0_m0_wo0_wi0_delayr28_q, ena => xIn_v(0), clk => clk, aclr => areset );

	--d_u0_m0_wo0_wi0_delayr28_q_11(DELAY,319)@10
    d_u0_m0_wo0_wi0_delayr28_q_11 : dspba_delay
    GENERIC MAP ( width => 7, depth => 1 )
    PORT MAP ( xin => u0_m0_wo0_wi0_delayr28_q, xout => d_u0_m0_wo0_wi0_delayr28_q_11_q, clk => clk, aclr => areset );

	--u0_m0_wo0_mtree_mult1_12_add_1(ADD,274)@11
    u0_m0_wo0_mtree_mult1_12_add_1_a <= STD_LOGIC_VECTOR((8 downto 7 => d_u0_m0_wo0_wi0_delayr28_q_11_q(6)) & d_u0_m0_wo0_wi0_delayr28_q_11_q);
    u0_m0_wo0_mtree_mult1_12_add_1_b <= STD_LOGIC_VECTOR((8 downto 8 => u0_m0_wo0_mtree_mult1_12_shift0_q(7)) & u0_m0_wo0_mtree_mult1_12_shift0_q);
    u0_m0_wo0_mtree_mult1_12_add_1: PROCESS (clk, areset)
    BEGIN
        IF (areset = '1') THEN
            u0_m0_wo0_mtree_mult1_12_add_1_o <= (others => '0');
        ELSIF(clk'EVENT AND clk = '1') THEN
            u0_m0_wo0_mtree_mult1_12_add_1_o <= STD_LOGIC_VECTOR(SIGNED(u0_m0_wo0_mtree_mult1_12_add_1_a) + SIGNED(u0_m0_wo0_mtree_mult1_12_add_1_b));
        END IF;
    END PROCESS;
    u0_m0_wo0_mtree_mult1_12_add_1_q <= u0_m0_wo0_mtree_mult1_12_add_1_o(8 downto 0);


	--u0_m0_wo0_mtree_mult1_12_shift2(BITSHIFT,275)@12
    u0_m0_wo0_mtree_mult1_12_shift2_q_int <= u0_m0_wo0_mtree_mult1_12_add_1_q & "0000";
    u0_m0_wo0_mtree_mult1_12_shift2_q <= u0_m0_wo0_mtree_mult1_12_shift2_q_int(12 downto 0);

	--u0_m0_wo0_mtree_add0_6(ADD,136)@12
    u0_m0_wo0_mtree_add0_6_a <= STD_LOGIC_VECTOR((14 downto 13 => u0_m0_wo0_mtree_mult1_12_shift2_q(12)) & u0_m0_wo0_mtree_mult1_12_shift2_q);
    u0_m0_wo0_mtree_add0_6_b <= STD_LOGIC_VECTOR((14 downto 14 => u0_m0_wo0_mtree_mult1_13_add_3_q(13)) & u0_m0_wo0_mtree_mult1_13_add_3_q);
    u0_m0_wo0_mtree_add0_6: PROCESS (clk, areset)
    BEGIN
        IF (areset = '1') THEN
            u0_m0_wo0_mtree_add0_6_o <= (others => '0');
        ELSIF(clk'EVENT AND clk = '1') THEN
            u0_m0_wo0_mtree_add0_6_o <= STD_LOGIC_VECTOR(SIGNED(u0_m0_wo0_mtree_add0_6_a) + SIGNED(u0_m0_wo0_mtree_add0_6_b));
        END IF;
    END PROCESS;
    u0_m0_wo0_mtree_add0_6_q <= u0_m0_wo0_mtree_add0_6_o(14 downto 0);


	--u0_m0_wo0_mtree_add1_3(ADD,153)@13
    u0_m0_wo0_mtree_add1_3_a <= STD_LOGIC_VECTOR((16 downto 15 => u0_m0_wo0_mtree_add0_6_q(14)) & u0_m0_wo0_mtree_add0_6_q);
    u0_m0_wo0_mtree_add1_3_b <= STD_LOGIC_VECTOR((16 downto 16 => u0_m0_wo0_mtree_add0_7_q(15)) & u0_m0_wo0_mtree_add0_7_q);
    u0_m0_wo0_mtree_add1_3: PROCESS (clk, areset)
    BEGIN
        IF (areset = '1') THEN
            u0_m0_wo0_mtree_add1_3_o <= (others => '0');
        ELSIF(clk'EVENT AND clk = '1') THEN
            u0_m0_wo0_mtree_add1_3_o <= STD_LOGIC_VECTOR(SIGNED(u0_m0_wo0_mtree_add1_3_a) + SIGNED(u0_m0_wo0_mtree_add1_3_b));
        END IF;
    END PROCESS;
    u0_m0_wo0_mtree_add1_3_q <= u0_m0_wo0_mtree_add1_3_o(16 downto 0);


	--u0_m0_wo0_wi0_delayr29(DELAY,36)@10
    u0_m0_wo0_wi0_delayr29 : dspba_delay
    GENERIC MAP ( width => 7, depth => 1 )
    PORT MAP ( xin => u0_m0_wo0_wi0_delayr28_q, xout => u0_m0_wo0_wi0_delayr29_q, ena => xIn_v(0), clk => clk, aclr => areset );

	--d_u0_m0_wo0_wi0_delayr29_q_11(DELAY,320)@10
    d_u0_m0_wo0_wi0_delayr29_q_11 : dspba_delay
    GENERIC MAP ( width => 7, depth => 1 )
    PORT MAP ( xin => u0_m0_wo0_wi0_delayr29_q, xout => d_u0_m0_wo0_wi0_delayr29_q_11_q, clk => clk, aclr => areset );

	--u0_m0_wo0_mtree_mult1_11_shift2(BITSHIFT,278)@11
    u0_m0_wo0_mtree_mult1_11_shift2_q_int <= d_u0_m0_wo0_wi0_delayr29_q_11_q & "00000";
    u0_m0_wo0_mtree_mult1_11_shift2_q <= u0_m0_wo0_mtree_mult1_11_shift2_q_int(11 downto 0);

	--u0_m0_wo0_mtree_mult1_11_shift0(BITSHIFT,276)@10
    u0_m0_wo0_mtree_mult1_11_shift0_q_int <= u0_m0_wo0_wi0_delayr29_q & "00";
    u0_m0_wo0_mtree_mult1_11_shift0_q <= u0_m0_wo0_mtree_mult1_11_shift0_q_int(8 downto 0);

	--u0_m0_wo0_mtree_mult1_11_add_1(ADD,277)@10
    u0_m0_wo0_mtree_mult1_11_add_1_a <= STD_LOGIC_VECTOR((9 downto 7 => u0_m0_wo0_wi0_delayr29_q(6)) & u0_m0_wo0_wi0_delayr29_q);
    u0_m0_wo0_mtree_mult1_11_add_1_b <= STD_LOGIC_VECTOR((9 downto 9 => u0_m0_wo0_mtree_mult1_11_shift0_q(8)) & u0_m0_wo0_mtree_mult1_11_shift0_q);
    u0_m0_wo0_mtree_mult1_11_add_1: PROCESS (clk, areset)
    BEGIN
        IF (areset = '1') THEN
            u0_m0_wo0_mtree_mult1_11_add_1_o <= (others => '0');
        ELSIF(clk'EVENT AND clk = '1') THEN
            u0_m0_wo0_mtree_mult1_11_add_1_o <= STD_LOGIC_VECTOR(SIGNED(u0_m0_wo0_mtree_mult1_11_add_1_a) + SIGNED(u0_m0_wo0_mtree_mult1_11_add_1_b));
        END IF;
    END PROCESS;
    u0_m0_wo0_mtree_mult1_11_add_1_q <= u0_m0_wo0_mtree_mult1_11_add_1_o(9 downto 0);


	--u0_m0_wo0_mtree_mult1_11_add_3(ADD,279)@11
    u0_m0_wo0_mtree_mult1_11_add_3_a <= STD_LOGIC_VECTOR((12 downto 10 => u0_m0_wo0_mtree_mult1_11_add_1_q(9)) & u0_m0_wo0_mtree_mult1_11_add_1_q);
    u0_m0_wo0_mtree_mult1_11_add_3_b <= STD_LOGIC_VECTOR((12 downto 12 => u0_m0_wo0_mtree_mult1_11_shift2_q(11)) & u0_m0_wo0_mtree_mult1_11_shift2_q);
    u0_m0_wo0_mtree_mult1_11_add_3: PROCESS (clk, areset)
    BEGIN
        IF (areset = '1') THEN
            u0_m0_wo0_mtree_mult1_11_add_3_o <= (others => '0');
        ELSIF(clk'EVENT AND clk = '1') THEN
            u0_m0_wo0_mtree_mult1_11_add_3_o <= STD_LOGIC_VECTOR(SIGNED(u0_m0_wo0_mtree_mult1_11_add_3_a) + SIGNED(u0_m0_wo0_mtree_mult1_11_add_3_b));
        END IF;
    END PROCESS;
    u0_m0_wo0_mtree_mult1_11_add_3_q <= u0_m0_wo0_mtree_mult1_11_add_3_o(12 downto 0);


	--u0_m0_wo0_mtree_mult1_10_shift0(BITSHIFT,280)@10
    u0_m0_wo0_mtree_mult1_10_shift0_q_int <= u0_m0_wo0_wi0_delayr30_q & "00";
    u0_m0_wo0_mtree_mult1_10_shift0_q <= u0_m0_wo0_mtree_mult1_10_shift0_q_int(8 downto 0);

	--u0_m0_wo0_wi0_delayr30(DELAY,37)@10
    u0_m0_wo0_wi0_delayr30 : dspba_delay
    GENERIC MAP ( width => 7, depth => 1 )
    PORT MAP ( xin => u0_m0_wo0_wi0_delayr29_q, xout => u0_m0_wo0_wi0_delayr30_q, ena => xIn_v(0), clk => clk, aclr => areset );

	--u0_m0_wo0_mtree_mult1_10_add_1(ADD,281)@10
    u0_m0_wo0_mtree_mult1_10_add_1_a <= STD_LOGIC_VECTOR((9 downto 7 => u0_m0_wo0_wi0_delayr30_q(6)) & u0_m0_wo0_wi0_delayr30_q);
    u0_m0_wo0_mtree_mult1_10_add_1_b <= STD_LOGIC_VECTOR((9 downto 9 => u0_m0_wo0_mtree_mult1_10_shift0_q(8)) & u0_m0_wo0_mtree_mult1_10_shift0_q);
    u0_m0_wo0_mtree_mult1_10_add_1: PROCESS (clk, areset)
    BEGIN
        IF (areset = '1') THEN
            u0_m0_wo0_mtree_mult1_10_add_1_o <= (others => '0');
        ELSIF(clk'EVENT AND clk = '1') THEN
            u0_m0_wo0_mtree_mult1_10_add_1_o <= STD_LOGIC_VECTOR(SIGNED(u0_m0_wo0_mtree_mult1_10_add_1_a) + SIGNED(u0_m0_wo0_mtree_mult1_10_add_1_b));
        END IF;
    END PROCESS;
    u0_m0_wo0_mtree_mult1_10_add_1_q <= u0_m0_wo0_mtree_mult1_10_add_1_o(9 downto 0);


	--d_u0_m0_wo0_wi0_delayr30_q_11(DELAY,321)@10
    d_u0_m0_wo0_wi0_delayr30_q_11 : dspba_delay
    GENERIC MAP ( width => 7, depth => 1 )
    PORT MAP ( xin => u0_m0_wo0_wi0_delayr30_q, xout => d_u0_m0_wo0_wi0_delayr30_q_11_q, clk => clk, aclr => areset );

	--u0_m0_wo0_mtree_mult1_10_shift2(BITSHIFT,282)@11
    u0_m0_wo0_mtree_mult1_10_shift2_q_int <= d_u0_m0_wo0_wi0_delayr30_q_11_q & "00000";
    u0_m0_wo0_mtree_mult1_10_shift2_q <= u0_m0_wo0_mtree_mult1_10_shift2_q_int(11 downto 0);

	--u0_m0_wo0_mtree_mult1_10_sub_3(SUB,283)@11
    u0_m0_wo0_mtree_mult1_10_sub_3_a <= STD_LOGIC_VECTOR((12 downto 12 => u0_m0_wo0_mtree_mult1_10_shift2_q(11)) & u0_m0_wo0_mtree_mult1_10_shift2_q);
    u0_m0_wo0_mtree_mult1_10_sub_3_b <= STD_LOGIC_VECTOR((12 downto 10 => u0_m0_wo0_mtree_mult1_10_add_1_q(9)) & u0_m0_wo0_mtree_mult1_10_add_1_q);
    u0_m0_wo0_mtree_mult1_10_sub_3: PROCESS (clk, areset)
    BEGIN
        IF (areset = '1') THEN
            u0_m0_wo0_mtree_mult1_10_sub_3_o <= (others => '0');
        ELSIF(clk'EVENT AND clk = '1') THEN
            u0_m0_wo0_mtree_mult1_10_sub_3_o <= STD_LOGIC_VECTOR(SIGNED(u0_m0_wo0_mtree_mult1_10_sub_3_a) - SIGNED(u0_m0_wo0_mtree_mult1_10_sub_3_b));
        END IF;
    END PROCESS;
    u0_m0_wo0_mtree_mult1_10_sub_3_q <= u0_m0_wo0_mtree_mult1_10_sub_3_o(12 downto 0);


	--u0_m0_wo0_mtree_add0_5(ADD,135)@12
    u0_m0_wo0_mtree_add0_5_a <= STD_LOGIC_VECTOR((13 downto 13 => u0_m0_wo0_mtree_mult1_10_sub_3_q(12)) & u0_m0_wo0_mtree_mult1_10_sub_3_q);
    u0_m0_wo0_mtree_add0_5_b <= STD_LOGIC_VECTOR((13 downto 13 => u0_m0_wo0_mtree_mult1_11_add_3_q(12)) & u0_m0_wo0_mtree_mult1_11_add_3_q);
    u0_m0_wo0_mtree_add0_5: PROCESS (clk, areset)
    BEGIN
        IF (areset = '1') THEN
            u0_m0_wo0_mtree_add0_5_o <= (others => '0');
        ELSIF(clk'EVENT AND clk = '1') THEN
            u0_m0_wo0_mtree_add0_5_o <= STD_LOGIC_VECTOR(SIGNED(u0_m0_wo0_mtree_add0_5_a) + SIGNED(u0_m0_wo0_mtree_add0_5_b));
        END IF;
    END PROCESS;
    u0_m0_wo0_mtree_add0_5_q <= u0_m0_wo0_mtree_add0_5_o(13 downto 0);
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
